Rustem666666/GyverNightLamp/firmware/Schemes/Lamp+TM1637+DFplayer + IR2 + USB  + DS3231 (ESP32).png

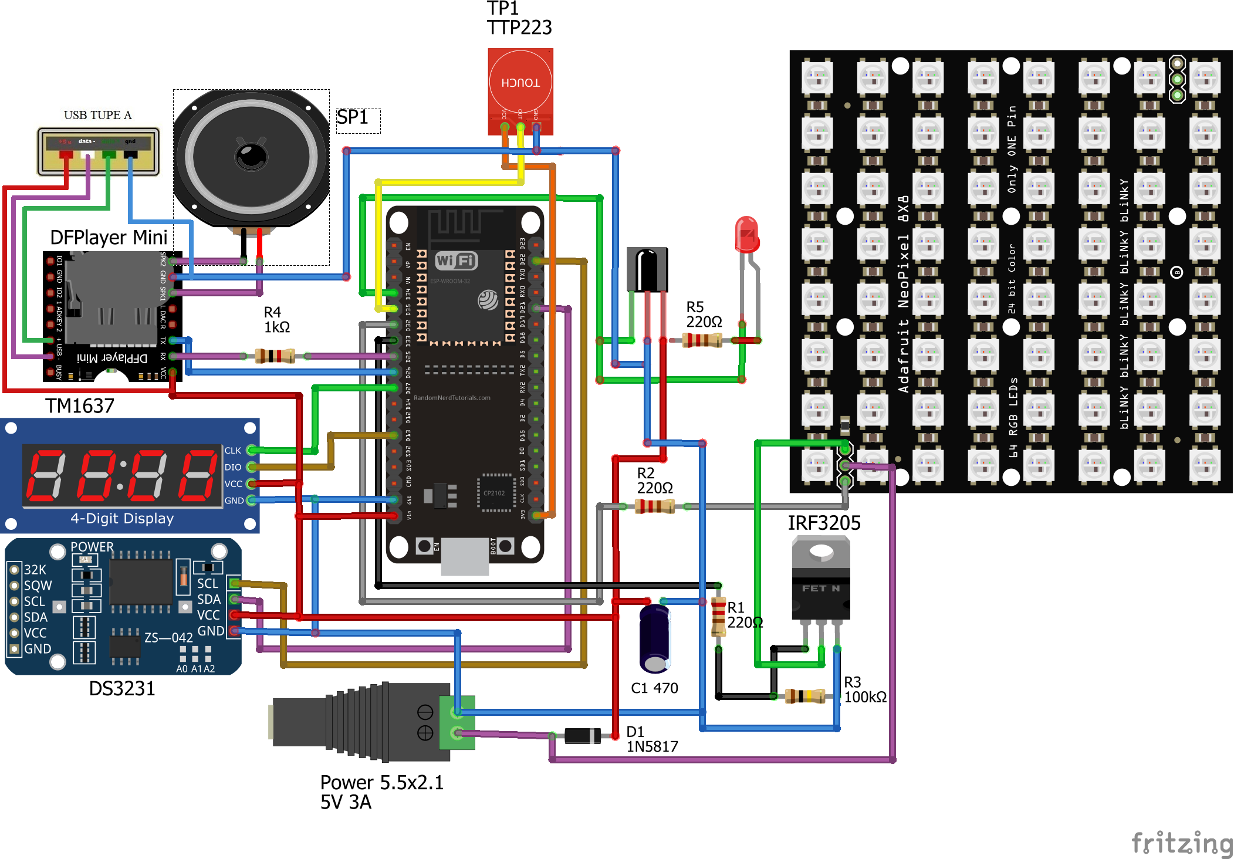
firmware/Schemes/Lamp+TM1637+DFplayer + IR2 + USB + DS3231 (ESP32).png
