Rustem666666/GyverNightLamp/firmware/FieryLedLamp/Constants.h

// Текущая версия : FieryLedLamp v5.4 132 эффекта
// ВНИМАНИЕ!!! Большая часть настроек перенесена в файл data/config и может изменяться в процессе эксплуатации лампы.
// Внимательно читайте файл ПРОЧТИ МЕНЯ!!!.txt и ПРОЧТИ МЕНЯ.doc (тут с картинками)

#pragma once

#define FLL_VERSION           (" Ver.5.4.132")


// ==========  ВНЕШНЕЕ УПРАВЛЕНИЕ  ===============
#define USE_MQTT                    (false)                  // true – используется mqtt клиент, false – нет
#if USE_MQTT
#define MQTT_RECONNECT_TIME   (10U)                         // Время в секундах перед подключением к брокеру MQTT в случае потери подключения
#endif
//#define USE_BLYNK  ("сюда_вставить_токен_из_приложения")  // раскомментируйте эту строку, если вы используете приложение Blynk (для iOS и Android) https://community.alexgyver.ru/threads/nastrojka-programmy-blynk-dlja-fiery-led-lamp.7787/

// =======  МОДУЛИ, ИСПОЛЬЗУЕМЫЕ  ==========
//#define ESP_USE_BUTTON                                      // Закомментировать, если кнопка не используется ((иначе лампа может регистрировать "фантомные" нажатия и некорректно устанавливать яркость)отключается на web странице)
//#define TM1637_USE                                          // Закомментировать, если не используется дисплей TM1637
//#define MP3_PLAYER_USE                                      // Закомментировать, если не используется плеер
//#define IR_RECEIVER_USE                                     // Закомментировать, если не используется ИК ДУ
//#define USE_RTC                                           // Закомментировать, если не используется RTC модуль
#ifdef USE_RTC
#define RTC_3231                                            

#endif
#ifdef TM1637_USE
  #define RTC_ATTACHED_TO_TM                                // для экономии пинов, DS3231 подключается параллельно TM1637
#endif

// =============  НАСТРОЙКА  ====================
#define USE_DEFAULT_SETTINGS_RESET                          // Закомментируйте эту строку, если не требуется, чтобы при загрузке списка эффектов с лампы настройки эффектов смахивали на значение по умолчанию

#define USE_MULTIPLE_LAMPS_CONTROL                          // Добавить код для управления несколькими лампами

//#define MP3_DEBUG                                         // если строка не закомментирована, выводятся отладочные сообщения mp3 player
//#define HEAP_SIZE_PRINT                                   // если строка не закомментирована, будет выводиться размер "купи" (свободного ОЗУ)
//#define GENERAL_DEBUG                                     // если строка не закомментирована, будут выводиться общие отладочные сообщения
#ifdef GENERAL_DEBUG
 //#define MAIN_CYCLES_PER_SECOND                           // Выводит количество главных циклов в секунду. Приблизительно то же, что и FPS. Будет выводиться только вместе с GENERAL_DEBUG
#endif

#define USE_LittleFS                                        // Закомментируйте эту строку, если вместо файловой системы LittlFS хотите использовать файловую систему SPIFFS (устаревшая)

// --- НАСТРОЙКА МР3 ПЛЕЕРА -------------
#ifdef MP3_PLAYER_USE
  //#define CHECK_MP3_CONNECTION                            // Закомментируйте эту строку, если нужно, чтобы лампа не проверяла наличие связи с MP3 плеером.
  //#define DF_PLAYER_IS_ORIGINAL                           // Если используется проигрыватель с чипом, отличным от AS20HGN402, закомментируйте эту строку
  #ifndef  DF_PLAYER_IS_ORIGINAL
    //#define DF_PLAYER_GD3200x                             // Если у вас такой чип в плеере и эта строка не закомментирована, то для озвучивания времени используются разные голоса.
  #endif  //DF_PLAYER_IS_ORIGINAL
#endif  //MP3_PLAYER_USE

// --- НАСТРОЙКА КНОПКИ -----------------
#define BUTTON_CAN_SET_SLEEP_TIMER                          // с этой строчкой, если на лампе набить кнопкой 4х кратно (один раз), лампа мигнёт дважды синим и если она выключена , то включится.
                                                            // Таймер выключения лампы будет установлен на BUTTON_SET_SLEEP_TIMER1 минут. Если на лампе набить кнопкой 3х кратно + удержание 4го нажатия, лампа мигнёт синим трижды и если она выключена , то включится.
                                                            // Таймер выключения лампы будет установлен на BUTTON_SET_SLEEP_TIMER2 минут. Чтобы убрать эту функцию, удалите или закомментируйте эту строчку
#ifdef BUTTON_CAN_SET_SLEEP_TIMER
  #define BUTTON_SET_SLEEP_TIMER1   (5UL)                   
  #define BUTTON_SET_SLEEP_TIMER2   (10UL)
#endif
#define BUTTON_IS_SENSORY     (1)                           // Если у вас не сенсорная, а простая кнопка, поменяйте в этой строке 1 на 0
#define BUTTON_LOCK_ON_START                                // с этой строкой, если в момент включения лампы в розетку успеть нажать кнопку или если вы забудете кнопку подключить, лампа отключит реакцию нажатия кнопки до следующего раза
#ifdef ESP_USE_BUTTON
#define DISPLAY_IP_AT_START                                 // Закомментируйте эту строку, если хотите, чтобы при включении питания и подключении к WiFi лампа один раз выводила свой IP адрес (для ламп с кнопкой)
#else
#define DISPLAY_IP_AT_START                                 // Закомментируйте эту строку, если не хотите, чтобы при включении питания и подключении к WiFi лампа один раз выводила свой IP адрес (для ламп без кнопки)
#endif  //ESP_USE_BUTTON
#if defined (ESP_USE_BUTTON)
#define BUTTON_STEP_TIMEOUT   (100U)                        // каждые BUTTON_STEP_TIMEOUT мс будет генерироваться событие удерживания кнопки (для регулировки яркости)
#define BUTTON_CLICK_TIMEOUT  (500U)                        // максимальное время между нажатиями кнопки в мс, до достижения которого считается серия последовательных нажатий
#if (BUTTON_IS_SENSORY == 1)
  #define BUTTON_SET_DEBOUNCE   (10U)                       // Время антидребезга mS для сенсорной кнопки
#else
  #define BUTTON_SET_DEBOUNCE   (60U)                       // Время антидребезга mS для механической кнопки
#endif
#endif

// --- ВРЕМЯ ---------------------------
#define GET_TIME_FROM_PHONE (5U)                            // с этой строчкой время в лампе само синхронизируется с приложением, когда лампа не имеет или потеряла доступ в интернет на сервер точного времени .
                                                            // для этого нужно использовать приложение FireLamp версии 3.0 или выше, либо другое приложение, которое отправляет время телефона в лампу. 
                                                            // цифра 5U означает, что синхранизация не чаще, чем раз в 5 минут. переход на зимнее время произойдёт только если изменение пришло со смартфона!
#define PHONE_N_MANUAL_TIME_PRIORITY                        // с этой строчкой, если время получено через приложение, то попытки синхронизации с NTP-сервером прекращаются (пригодится тем, у кого возникают проблемы с NTP-сервером)
#define WARNING_IF_NO_TIME      (7U)                        // с этой строчкой лампа будет подмигивать в нижнем ряде светодиодов, когда она не знает, сколько сейчас времени.
                                                            // 7 - это яркость мигающих точек (максимум - 255U), когда лампа выключена
//#define WARNING_IF_NO_TIME_ON_EFFECTS_TOO                 // а если эту строку раскомментировать, то подмигивание будет даже во время работы эффектов. яркость точек будет, как у работающего эффекта
#define USE_NTP                                             // закомментировать или удалить эту строку, если нужно, чтобы лампа не обращалась в интернет на сервер времени (NTP-сервер).
                                                            // Стоит её убрать только в том случае, если в вашей домашней сети нет круглосуточного доступа в интернет.
                                                            // Лампу можно отправить в другой часовой пояс, так как часовой пояс, выставляется на web странице. 
                                                            // Там же чекбоксом выбирается необходимость перехода на летнее время.
#define NTP_INTERVAL          (59 * 60UL * 1000UL)          // интервал синхронизации времени (59 минут)
                                                            // константы DAY_HOURS_BRIGHTNESS и NIGHT_HOURS_BRIGHTNESS используются только, когда матрица выключена, иначе будет использована яркость текущего эффекта
// --- Яркость вспышки ПРЕДУПРЕЖДЕНИЕ showWarning ---
#define WARNING_BRI_DAY    (10U)                            // Яркость вспышки предупреждение днем
#define WARNING_BRI_NIGHT    (5U)                           // Яркость вспышки предупреждения ночью

// --- МАТРИЦА -------------------------
#define CURRENT_LIMIT         (2000U)                       // Лимит потребления матрицы по току в миллиамперах, автоматически управляет яркостью (пожалей свой блок питания!) 0 – выключить лимит

#define WIDTH                 (16)                          // ширина матрицы
#define HEIGHT                (8)                          // высота матрицы

#define COLOR_ORDER           (GRB)                         // порядок цветов на ленте. Если цвет отображается некорректно - меняйте. Начать можно с RGB

// --- РАЗНОЕ -----------------------------
#define ESP_CONF_TIMEOUT        (60U)                       // Время в секундах, которое лампа будет ждать от вас ввода пароля для ОТА обновления (пароль совпадает с паролем точки доступа)
#define INTERNET_CHECK_PERIOD   (60UL)                      // Период повторной проверки наличия интернета в секундах


// ========  РАЗДЕЛЕНИЕ КОНТАКТОВ МОДУЛЯ  ==================================================

// --- ESP_PIN_OUT ESP32 ---  РАЗДЕЛЕНИЕ КОНТАКТОВ МОДУЛЯ ESP32 (ESP8266 смотри ниже) -----
#ifdef ESP32_USED
#define LED_PIN               (32U)                         // Пин ленты
#define BTN_PIN               (35U)                         // Пин кнопки

#define I2C_SDA               (21U)                         // DS3231 SDA pin
#define I2C_SCL               (22U)                         // DS3231 SCL pin

#define MOSFET_PIN            (33U)                         // Пин MOSFET транзистора - может использоваться для управления питанием матрицы/ленты (если раскомментирована строка)
#define MOSFET_LEVEL          (HIGH)                        // логический уровень, в который будет установлен пен MOSFET_PIN, когда матрица включена - HIGH или LOW (если раскомментировать)
//#define ALARM_PIN             (39U)                       // пен состояния будильника – может быть использован для управления любым внешним устройством на время работы будильника (если раскомментировать)
//#define ALARM_LEVEL           (HIGH)                      // логический уровень, в который будет установлен пен ALARM_PIN, когда "рассвет"/будильник включен (если раскомментировать)

#ifdef TM1637_USE
#define DIO                   (13U)                         // TM1637 display DIO pin
#define CLK                   (27U)                         // TM1637 display CLK pin
#endif  //TM1637_USE

#ifdef MP3_PLAYER_USE
 #define MP3_TX_PIN            (25U)                        // Определяет пин TX (RX на плеере) последовательного порта
 #define MP3_RX_PIN            (26U)                        // Определяет пин RX (TX на плеере) последовательного порта
 #endif //MP3_PLAYER_USE
 
#ifdef IR_RECEIVER_USE
  #define IR_RECEIVER_PIN     (34U)                         // Пин ИК сенсора
#endif  //IR_RECEIVER_USE

#else
// --- ESP_PIN_OUT ESP8266 ---  РАЗДЕЛЕНИЕ КОНТАКТОВ МОДУЛЯ ESP8266 (ESP32 смотри выше) ---
#define LED_PIN               (0U)                          // Пин ленты                (D3) 
#define BTN_PIN               (4U)                          // Пин кнопки               (D2)

#define MOSFET_PIN            (16U)                         // Пин MOSFET транзистора (D0) - может использоваться для управления питанием матрицы/ленты (если раскомментирована строка)
#define MOSFET_LEVEL          (HIGH)                        // логический уровень, в который будет установлен пен MOSFET_PIN, когда матрица включена - HIGH или LOW (если раскомментировать)
//#define ALARM_PIN             (15U)                       // Пин состояния будильника – может быть использован для управления любым внешним устройством на время работы будильника (если раскомментировать)
//#define ALARM_LEVEL           (HIGH)                      // логический уровень, в который будет установлен пен ALARM_PIN, когда "рассвет"/будильник включен (если раскомментировать)

#ifdef TM1637_USE
  #define DIO                   (14U)                       // TM1637 DIO на pin (D5)
  #define CLK                   (5U)                        // TM1637 CLK на pin (D1)
#endif  //TM1637_USE

#ifdef RTC_ATTACHED_TO_TM
  #define I2C_SDA               (CLK)
  #define I2C_SCL               (DIO)
#else
  #define I2C_SDA               (5U)                        // DS3231 SDA на GPIO5 (D1)
  #define I2C_SCL               (14U)                       // DS3231 SCL на GPIO14 (D5)
#endif

#ifdef MP3_PLAYER_USE
 #define MP3_TX_PIN            (12U)                        // Определяет пин (D6) TX (RX на плеере) последовательного порта
 #define MP3_RX_PIN            (13U)                        // Определяет пин (D7) RX (TX на плеере) последовательного порта
 #endif //MP3_PLAYER_USE

#ifdef IR_RECEIVER_USE
  #define IR_RECEIVER_PIN     (2U)                          //Пин ИК сенсора D4
#endif  //IR_RECEIVER_USE
#endif

// ==================================================================================================
//#define CONNECTION_ANGLE      (0U)                        // угол подключения: 0 - левый нижний, 1 - левый верхний, 2 - правый верхний, 3 - правый нижний
//#define STRIP_DIRECTION       (0U)                        // направление ленты из угла: 0 - вправо, 1 - вверх, 2 - влево, 3 - вниз
                                                            // при неправильной настройке матрицы вы получите предупреждение "Wrong matrix parameters! Set to default"
// Не используется.                                         // шпаргалка по настройке матрицы здесь: https://alexgyver.ru/wp-content/uploads/2018/11/scheme3.jpg
// Это настраивается в веб-интерфейсе.                      // (но в ней, кажется, перепутаны местами квадратики в 4м столбце, а может, и ещё какие-то)

// =========  ЭФФЕКТЫ  =======================================================================
// == названия и номера эффектов ниже в списке используются на вкладке effectTricker ==
// == если меняете, меняйте и там, и ещё здесь ниже в РЕЕСТРЕ ДОСТУПНЫХ ЭФФЕКТОВ ==

#define EFF_WHITE_COLOR         (  0U)    // Бeлый cвeт
#define EFF_AVRORA              (  1U)    // Аврора
#define EFF_WATERCOLOR          (  2U)    // Акварель
#define EFF_FLOWERRUTA          (  3U)    // Аленький цветочек
#define EFF_BUTTERFLY           (  4U)    // Бабочка
#define EFF_EFF_POOL            (  5U)    // Бассейн
#define EFF_BAMBOO              (  6U)    // Бамбук
#define EFF_MADNESS             (  7U)    // Безумие
#define EFF_BALLROUTINE         (  8U)    // Блуждающий кубик
#define EFF_WATERFALL           (  9U)    // Водопад
#define EFF_WATERFALL_4IN1      ( 10U)    // Водопад 4в1
#define EFF_WAVES               ( 11U)    // Волны
#define EFF_MAGICLANTERN        ( 12U)    // Волшебный Фонарик
#define EFF_WINE                ( 13U)    // Вино
#define EFF_WHIRL               ( 14U)    // Вихри пламени
#define EFF_WHIRL_MULTI         ( 15U)    // Вихри разноцветные
#define EFF_STARFALL            ( 16U)    // Вьюга
#define EFF_STORMY_RAIN         ( 17U)    // Гроза в банке
#define EFF_DNA                 ( 18U)    // ДНК
#define EFF_SMOKE               ( 19U)    // Дым
#define EFF_SMOKE_COLOR         ( 20U)    // Дым разноцветный
#define EFF_SMOKEBALLS          ( 21U)    // Дымовые шашки
#define EFF_LIQUIDLAMP          ( 22U)    // Жидкая лампа
#define EFF_LIQUIDLAMP_AUTO     ( 23U)    // Жидкая лампа авто
#define EFF_SWIRL               ( 24U)    // Завиток
#define EFF_STARS               ( 25U)    // Звезды
#define EFF_NEW_STARS           ( 26U)    // Звезды Новые
#define EFF_ZEBRA               ( 27U)    // Зебра
#define EFF_TIXYLAND            ( 28U)    // Земля Тикси
#define EFF_SNAKES              ( 29U)    // Змейки
#define EFF_FOUNTAIN            ( 30U)    // Источник
#define EFF_DROP_IN_WATER       ( 31U)    // Капли на воде
#define EFF_DROPS               ( 32U)    // Капли на стекле
#define EFF_LLAND               ( 33U)    // Кипение
#define EFF_RINGS               ( 34U)    // Кодовый замок
#define EFF_COMET               ( 35U)    // Комета
#define EFF_COMET_COLOR         ( 36U)    // Комета одноцветная
#define EFF_COMET_TWO           ( 37U)    // Комета двойная
#define EFF_COMET_THREE         ( 38U)    // Комета тройная
#define EFF_CONTACTS            ( 39U)    // Контакты
#define EFF_SPARKLES            ( 40U)    // Конфетти
#define EFF_CUBE2D              ( 41U)    // Кубик Рубика
#define EFF_LAVA                ( 42U)    // Лава
#define EFF_LAVALAMP            ( 43U)    // Лавовая лампа
#define EFF_BUTTERFLYS_LAMP     ( 44U)    // Лампа с мотыльками
#define EFF_FOREST              ( 45U)    // Лес
#define EFF_LUMENJER            ( 46U)    // Люмeньep
#define EFF_MAGMA               ( 47U)    // Магма
#define EFF_PAINTS              ( 48U)    // Масляные краски
#define EFF_MATRIX              ( 49U)    // Матрица
#define EFF_TWINKLES            ( 50U)    // Мерцание
#define EFF_METABALLS           ( 51U)    // Метоболз
#define EFF_WEB_TOOLS           ( 52U)    // Мечта дизайнера
#define EFF_MOSAIC              ( 53U)    // Мозайка
#define EFF_BUTTERFLYS          ( 54U)    // Moтыльки
#define EFF_BBALLS              ( 55U)    // Мячики
#define EFF_BALLS_BOUNCE        ( 56U)    // Мячики без границ
#define EFF_CHRISTMAS_TREE      ( 57U)    // Новогодняя Елка
#define EFF_NIGHTCITY           ( 58U)    // Ночной Город
#define EFF_FIRE                ( 59U)    // Огонь
#define EFF_FIRE_2012           ( 60U)    // Огонь 2012
#define EFF_FIRE_2018           ( 61U)    // Огонь 2018
#define EFF_FIRE_2020           ( 62U)    // Огонь 2020
#define EFF_FIRE_2021           ( 63U)    // Огонь 2021
#define EFF_FIREFLY_TOP         ( 64U)    // Огoнь верховой
#define EFF_FIREFLY             ( 65U)    // Огoнь парящий
#define EFF_FIRESPARKS          ( 66U)    // Огонь с искрами
#define EFF_COLOR_RAIN          ( 67U)    // Осадки
#define EFF_OSCILLATING         ( 68U)    // Осциллятор
#define EFF_CLOUDS              ( 69U)    // Облака
#define EFF_OCEAN               ( 70U)    // Океан
#define EFF_OCTOPUS             ( 71U)    // Осьминог
#define EFF_RAINBOW_STRIPE      ( 72U)    // Павлин
#define EFF_HOURGLASS           ( 73U)    // Песочные часы
#define EFF_PAINTBALL           ( 74U)    // Пейнтбол
#define EFF_PICASSO             ( 75U)    // Пикассо
#define EFF_PLASMA              ( 76U)    // Плазма
#define EFF_SPIDER              ( 77U)    // Плазменная лампа
#define EFF_PLASMA_WAVES        ( 78U)    // Плазменные волны
#define EFF_FLAME               ( 79U)    // Пламя
#define EFF_PLANETEARTH         ( 80U)    // Планета Земля
#define EFF_BY_EFFECT           ( 81U)    // Побочный эффект
#define EFF_POPCORN             ( 82U)    // Попкорн
#define EFF_PRISMATA            ( 83U)    // Призмата
#define EFF_ATTRACT             ( 84U)    // Притяжение
#define EFF_LEAPERS             ( 85U)    // Пpыгyны
#define EFF_PULSE               ( 86U)    // Пульс
#define EFF_PULSE_WHITE         ( 87U)    // Пульс белый
#define EFF_PULSE_RAINBOW       ( 88U)    // Пульс радужный
#define EFF_RADIAL_WAWE         ( 89U)    // Радиальная волна
#define EFF_RAINBOW_VER         ( 90U)    // Радуга
#define EFF_RAINBOW             ( 91U)    // Радуга 3D
#define EFF_RAINBOW_SPOT        ( 92U)    // Радужное Пятно
#define EFF_RAINBOW_RINGS       ( 93U)    // Радужные кольца
#define EFF_SNAKE               ( 94U)    // Радужный змей
#define EFF_RAIN                ( 95U)    // Разноцветный дождь
#define EFF_DANDELIONS          ( 96U)    // Разноцветные одуванчики
#define EFF_RIVERS              ( 97U)    // Реки Ботсваны
#define EFF_LIGHTERS            ( 98U)    // Светлячки
#define EFF_LIGHTER_TRACES      ( 99U)    // Светлячки со шлейфом
#define EFF_FEATHER_CANDLE      (100U)    // Свеча
#define EFF_AURORA              (101U)    // Северное сияние
#define EFF_SERPENTINE          (102U)    // Серпантин
#define EFF_SCANNER             (103U)    // Сканер
#define EFF_SINUSOID3           (104U)    // Синусоид
#define EFF_COLORS              (105U)    // Смена цвета
#define EFF_SNOW                (106U)    // Снегопад
#define EFF_SPECTRUM            (107U)    // Спектрум
#define EFF_SPIRO               (108U)    // Спирали
#define EFF_FLOCK               (109U)    // Стая
#define EFF_FLOCK_N_PR          (110U)    // Стая и хищник
#define EFF_ARROWS              (111U)    // Стрелки
#define EFF_STROBE              (112U)    // Строб.Хаос.Дифузия
#define EFF_SHADOWS             (113U)    // Тени
#define EFF_PACIFIC             (114U)    // Тихий океан
#define EFF_TORNADO             (115U)    // Торнадо
#define EFF_SIMPLE_RAIN         (116U)    // Tyчкa в банке
#define EFF_FIREWORK            (117U)    // Фейерверк
#define EFF_FIREWORK_2          (118U)    // Фейерверк 2
#define EFF_FAIRY               (119U)    // Фея
#define EFF_FONTAN              (120U)    // Фонтан
#define EFF_TRICOLOR            (121U)    // Флаг (Триколор)
#define EFF_COLOR               (122U)    // Цвет
#define EFF_EFF_COLORED_PYTHON  (123U)    // Цветной Питон
#define EFF_EFF_SAND            (124U)    // Цветные драже
#define EFF_COLOR_FRIZZLES      (125U)    // Цветные кудри
#define EFF_EFF_LOTUS           (126U)    // Цветок лотоса
#define EFF_TURBULENCE          (127U)    // Цифровая турбулентность
#define EFF_SPHERES             (128U)    // Шapы
#define EFF_NEXUS               (129U)    // Nexus
#define EFF_EFF_COLOR_FADED     (130U)    // Цвет с затуханием
#define EFF_CLOCK               (131U)    // Часы

#define MODE_AMOUNT         (132U)    // количество режимов

// ============= МАССИВ НАСТРОЕК ЭФФЕКТОВ ПО УМОЛЧАНИЮ ===================
// формат записи:
//{ Яркость, Скорость, Масштаб}

static const uint8_t defaultSettings[][3] PROGMEM = {
  {  10,   1,  50}, // Бeлый cвeт
  {  35,  90,  50}, // Аврора
  {  25, 200,  65}, // Акварель
  {  20, 215,  60}, // Аленький цветочек
  {  20,  11,   3}, // Бабочка
  {  25, 185,  63}, // Бассейн
  {  20, 215,  90}, // Бамбук
  {  35,  20,  60}, // Безумие
  {  20, 150,  50}, // Блуждающий кубик
  {  30, 212,  54}, // Водопад
  {  20, 195,  22}, // Водопад 4в1
  {  40, 233,  80}, // Волны
  {  45, 175,  60}, // Волшебный Фонарик
  {  80, 205,  40}, // Вино
  {  25, 210,   1}, // Вихри пламени
  {  20, 210,  86}, // Вихри разноцветные
  {  55, 191,  54}, // Вьюга
  {  40, 210,   8}, // Гроза в банке
  {  30,  80,  95}, // ДНК
  {  25, 195, 100}, // Дым
  {  25, 190,  30}, // Дым разноцветный
  {  30, 170,  25}, // Дымовые шашки
  {  20, 110,   1}, // Жидкая лампа
  {  20, 124,  39}, // Жидкая лампа авто
  {  30, 195,  70}, // Завиток
  {  25, 215,  99}, // Звезды
  {  25,  18,  26}, // Звезды Новые
  {  15,   8,  21}, // Зебра
  {  20, 212,  76}, // Земля Тикси
  {  20,  40,  15}, // Змейки
  {  25, 233,  30}, // Источник
  {  20, 200,  55}, // Капли на воде
  {  20,  40,  59}, // Капли на стекле
  {  15, 240,  18}, // Кипение
  {  30, 205,  91}, // Кодовый замок
  {  20, 205,  28}, // Комета
  {  20, 212,  69}, // Комета одноцветная
  {  25, 186,  19}, // Комета двойная
  {  25, 186,   9}, // Комета тройная
  {  25, 200,  60}, // Контакты
  {  30, 142,  63}, // Конфетти
  {  45, 222,  92}, // Кубик Рубика
  {  15,   9,  24}, // Лава
  {  15, 240,   1}, // Лавовая лампа
  {  30,  61,  20}, // Лампа с мотыльками
  {  15,  15,  95}, // Лес
  {  20, 200,  40}, // Люмeньep
  {  16, 205,  20}, // Магма
  {  15, 195,  50}, // Масляные краски
  {  25, 186,  23}, // Матрица
  {  25, 235,   4}, // Мерцание
  {  15,  72,   3}, // Метоболз
  {  28,  70,  20}, // Мечта дизайнера
  {  15, 205,  50}, // Мозайка
  {  20,  61,  20}, // Moтыльки
  {  15, 255,  26}, // Мячики
  {  25, 255,  85}, // Мячики без границ
  {  30, 165,  30}, // Новогодняя Елка
  {  35,  50,  25}, // Ночной Город
  {  25, 210,   1}, // Огонь
  {  15, 220,  63}, // Огонь 2012
  {  30, 220,  15}, // Огонь 2018
  {  20, 225,  11}, // Огонь 2020
  {  25, 150,  22}, // Огонь 2021
  {  26, 190,  15}, // Огoнь верховой
  {  30, 200,  15}, // Огoнь парящий
  {  30,  80,  64}, // Огонь с искрами
  {  20, 205, 149}, // Осадки
  {  15, 208, 100}, // Осциллятор
  {  20,  15,  34}, // Облака
  {  20,   8,  12}, // Океан
  {  15, 200,  51}, // Осьминог
  {  20,   5,  12}, // Павлин
  {  20, 150,   1}, // Песочные часы
  {  25, 195,   1}, // Пейнтбол
  {  15, 220,  40}, // Пикассо
  {  10,  20,  35}, // Плазма
  {  10,  30,  82}, // Плазменная лампа
  {  15,  15,  50}, // Плазменные волны
  {  30,  45,   3}, // Пламя
  {  25, 128,  75}, // Планета Земля
  {  40, 165,  30}, // Побочный эффект
  {  10,  70,  16}, // Попкорн
  {  15, 100,  88}, // Призмата
  {  20, 205,  65}, // Притяжение
  {  25, 203,   5}, // Пpыгyны
  {  20, 185,   6}, // Пульс
  {  20, 179,  11}, // Пульс белый
  {  20, 185,  31}, // Пульс радужный
  {  15, 220,  50}, // Радиальная волна
  {  10, 215,  50}, // Радуга
  {  10,  13,  60}, // Радуга 3D
  {  40, 200,  40}, // Радужное Пятно
  {  20, 128,  25}, // Радужные кольца
  {  15, 205, 100}, // Радужный змей
  {  15, 205,   1}, // Разноцветный дождь
  {  20,  50,  90}, // Разноцветные одуванчики
  {  12, 175,  50}, // Реки Ботсваны
  {  15, 180,  23}, // Светлячки
  {  15, 185,  93}, // Светлячки со шлейфом
  {  20, 220,   8}, // Свеча
  {  15, 160,  64}, // Северное сияние
  {  15,  75,  50}, // Серпантин
  {  50, 230,  40}, // Сканер
  {  20, 127,  75}, // Синусоид
  {  25, 240,   1}, // Смена цвета
  {  10, 205,  90}, // Снегопад
  {  25, 175, 100}, // Спектрум
  {  15,  45,   3}, // Спирали
  {  15, 136,   4}, // Стая
  {  15, 128,  80}, // Стая и хищник
  {  80, 165,  40}, // Стрелки
  {  25,   1,  45}, // Строб.Хаос.Дифузия
  {  50, 160,   1}, // Тени
  {  20, 127, 100}, // Тихий океан
  {  15, 127,  50}, // Торнадо
  {  50, 210,   2}, // Tyчкa в банке
  {  25, 180,  70}, // Фейерверк
  {  15, 240,  75}, // Фейерверк 2
  {  20, 212,  85}, // Фея
  {  40, 250,  75}, // Фонтан
  {  20,  55,  13}, // Флаг (Триколор)
  {  20, 240,  65}, // Цвет
  {  20, 127,  92}, // Цветной Питон
  {  15, 195,  80}, // Цветные драже
  {  25, 128,  60}, // Цветные кудри
  {  15, 150,  45}, // Цветок лотоса
  {  15, 215,  35}, // Цифровая турбулентность
  {  20,  50,   5}, // Шapы
  {  25,  85,  20}, // Nexus
  {   2,   1,   3}, // Цвет с затуханием
  {  30, 214,  80}  // Часы
}; // ^-- проверьте, чтобы у предыдущей строки не было запятой после скобки

// ------------ ОШИБАТЬСЯ НЕЛЬЗЯ!!!   ------------------------------------------------

// ============= КОНЕЦ МАССИВА =====

// === ОСТАЛЬНОЕ ДЛЯ РАЗРАБОТЧИКОВ =====

// --- МАТРИЦА -------------------------
// если у вас не обычная матрица, а сборка из ленты или гирлянда, и возникают непонятной природы артефакты в рисунке эффекта, попробуйте менять следующие три строчки
//#define FASTLED_ALLOW_INTERRUPTS      (1)                 // default: 1; // Используйте это, чтобы заставить FastLED разрешить прерывания в безтактовых наборах микросхем (или заставить его запретить), переопределив значение по умолчанию на платформах, которые это поддерживают. Установите значение 1, чтобы разрешить прерывания, или 0, чтобы их запретить.
#define FASTLED_INTERRUPT_RETRY_COUNT   (0)                 // default: 2; // Используйте это, чтобы определить, сколько раз FastLED попытается повторно передать кадр, если он слишком долго прерывается.
#ifdef ESP32_USED
 #define FASTLED_ESP32_RAW_PIN_ORDER
#else
 #define FASTLED_ESP8266_RAW_PIN_ORDER                      // FASTLED_ESP8266_RAW_PIN_ORDER, FASTLED_ESP8266_D1_PIN_ORDER or FASTLED_ESP8266_NODEMCU_PIN_ORDER
#endif

#define NUM_LEDS              (uint16_t)(WIDTH * HEIGHT)
#define SEGMENTS              (1U)                          // диодов в одном "пикселе" (для создания матрицы из кусков ленты). вряд ли эффекты будут корректно работать, если изменить этот параметр

#define DYNAMIC                (0U)   // динамическая задержка для кадров ( будет использоваться бегунок Скорость )
#define SOFT_DELAY             (1U)   // задержка для смены кадров FPSdelay задается програмно прямо в теле эффекта
#define LOW_DELAY             (15U)   // низкая фиксированная задержка для смены кадров
#define HIGH_DELAY            (50U)   // высокая фиксированная задержка для смены кадров
#define DYNAMIC_DELAY_TICK    if (millis() - effTimer >= (256U - modes[currentMode].Speed))
#define HIGH_DELAY_TICK       if (millis() - effTimer >= 50)
#define LOW_DELAY_TICK        if (millis() - effTimer >= 15)
#define MICRO_DELAY_TICK      if (millis() - effTimer >= 2)
#define SOFT_DELAY_TICK       if (millis() - effTimer >= FPSdelay)

#define BRIGHTNESS            (40U)                         // стандартная маскимальная яркость (0-255). используется только в момент включения питания лампы

#define ESP_HTTP_PORT         (80U)                         // номер порта, который будет использоваться во время первой утановки имени WiFi сети (и пароля), к которой потом будет подключаться лампа в режиме WiFi клиента (лучше не менять)
#define ESP_UDP_PORT          (8888U)                       // номер порта, который будет "слушать" UDP сервер во время работы лампы как в режиме WiFi точки доступа, так и в режиме WiFi клиента (лучше не менять)
#define WIFIMAN_DEBUG         (false)                       // вывод отладочных сообщений при подключении к WiFi сети: true - выводятся, false - не выводятся; настройка не зависит от GENERAL_DEBUG
#define OTA                                                 // если строка не закомментирована, модуль будет ждать два последовательных запроса пользователя на прошивку по воздуху (два четрёхкратных нажатия на кнопку)
#ifdef OTA
#define ESP_OTA_PORT          (8266U)                       // номер порта, который будет "прослушиваться" в ожидании команды прошивки по воздуху
#endif

#define RANDOM_SETTINGS_IN_CYCLE_MODE                       // Строка добавлена для совместимости файлов эффектов с версией  86 в 1 (или уже больше) от Сотнег.                                                             
                                                            // этот режим можно включать/выключать на web странице лампы или "секретной" командой. Не удаляйте и не комментируйте эту строку.
#define USE_RANDOM_SETS_IN_APP                              // Строка добавлена для совместимости файлов эффектов с версией  86 в 1 (или уже больше) от Сотнег.                               
                                                            // Этот режим уже поддерживается приложением от Котейка под Андроид. Не удаляйте и не комментируйте эту строку.
#define SUMMER_HOUR           (3U)                          // час (по зимнему времени!), когда заканчивается зимнее время и начинается летнее; [0..23]
#define SUMMER_WEEK_NUM       (week_t::Last)                // номер недели в месяце, когда происходит переход на летнее время (возможные варианты: First - первая, Second - вторая, Third - третья, Fourth - четвёртая, Last - последняя)
#define SUMMER_WEEKDAY        (dow_t::Sun)                  // день недели, когда происходит переход на летнее время (возможные варианты: Mon - пн, Tue - вт, Wed - ср, Thu - чт, Sat - сб, Sun - вс)
#define SUMMER_MONTH          (month_t::Mar)                // месяц, в котором происходит переход на летнее время (возможные варианты: Jan - январь, Feb - февраль, Mar - март, Apr - апрель, May - май, Jun - июнь, Jul - июль, Aug - август, Sep - сентябрь, Oct - октябрь, Nov - ноябрь, Dec - декабрь)
#define SUMMER_TIMEZONE_NAME  ("EEST")                      // обозначение летнего времени; до 5 символов; может быть использовано, если понадобится его вывести после вывода времени; может быть "ЛЕТ"
#define WINTER_HOUR           (4U)                          // час (по летнему времени!), когда заканчивается летнее время и начинается зимнее; [0..23]
#define WINTER_WEEK_NUM       (week_t::Last)                // номер недели в месяце, когда происходит переход на зимнее время (возможные варианты: First - первая, Second - вторая, Third - третья, Fourth - четвёртая, Last - последняя)
#define WINTER_WEEKDAY        (dow_t::Sun)                  // день недели, когда происходит переход на зимнее время (возможные варианты: Mon - пн, Tue - вт, Wed - ср, Thu - чт, Sat - сб, Sun - вс)
#define WINTER_MONTH          (month_t::Oct)                // месяц, в котором происходит переход на зимнее время (возможные варианты: Jan - январь, Feb - февраль, Mar - март, Apr - апрель, May - май, Jun - июнь, Jul - июль, Aug - август, Sep - сентябрь, Oct - октябрь, Nov - ноябрь, Dec - декабрь)
#define WINTER_TIMEZONE_NAME  ("EET")                       // обозначение зимнего времени; до 5 символов; может быть использовано, если понадобится его вывести после вывода времени; может быть "ЗИМ"


// --- РАССВЕТ -------------------------
uint8_t DAWN_BRIGHT ;                                       // максимальная яркость рассвета (0-255)
uint8_t DAWN_TIMEOUT;                                       // сколько рассвет светит после времени будильника, минут. Может быть изменено в установках будильника
// --- ЗАКАТ -------------------------
uint8_t SUNSET_BRIGHT ;                                     // максимальная яркость заката (0-255)


//#define MAX_UDP_BUFFER_SIZE (UDP_TX_PACKET_MAX_SIZE + 1)
// максимальный размер буффера UDP сервера 
// 255 - это максимальное значение, при котором работа с Избранным не будет глючить
// для исходящих сообщений в приложение данное ограничение можно обойти (см. как реализована отправка "LIST"),
// а для входящего списка избранного - хз. пришлось увеличить до максимально возможножного значения. 
// дальше придётся переделывать типы (размеры) переменных в функциях FavoritesManager.h
#define MAX_UDP_BUFFER_SIZE   (MODE_AMOUNT * 2 + 20)        // максимальный размер буффера UDP сервера

#define GENERAL_DEBUG_TELNET  (false)                       // true - отладочные сообщения будут выводиться в telnet вместо Serial порта (для удалённой отладки без подключения usb кабелем)
#define TELNET_PORT           (23U)                         // номер telnet порта

#if defined(GENERAL_DEBUG) && GENERAL_DEBUG_TELNET
WiFiServer telnetServer(TELNET_PORT);                       // telnet сервер
WiFiClient telnet;                                          // обработчик событий telnet клиента
bool telnetGreetingShown = false;                           // признак "показано приветствие в telnet"
#define LOG                   telnet
#else
#define LOG                   Serial
#endif

//================ Дальше только для разработчиков. Не меняйте здесь ничего, если не уверены в результате!!! ===================

//#include <EEPROM.h>
//#include "Types.h"
#define EEPROM_PASSWORD_START_ADDRESS           (0U)            // начальный адрес в EEPROM памяти для записи пароля к роутеру
#define EEPROM_MODES_START_ADDRESS              (0x50U)         // начальный адрес в EEPROM памяти для записи настроек эффектов (яркость, скорость, масштаб)
#define EEPROM_FIRST_RUN_ADDRESS                (0x40U)         // (0x40U) адрес в EEPROM памяти для записи признака первого запуска (определяет необходимость первоначальной записи всех хранимых настроек)
#define EEPROM_MODE_STRUCT_SIZE                 (3U)            // 1 байт - яркость; 1 байт - скорость; 1 байт - масштаб
#define EEPROM_TOTAL_BYTES_USED                 (EEPROM_MODES_START_ADDRESS+MODE_AMOUNT*EEPROM_MODE_STRUCT_SIZE+1)       
#define EEPROM_FIRST_RUN_MARK                   (MODE_AMOUNT-255) // число-метка, если ещё не записно в EEPROM_FIRST_RUN_ADDRESS, значит нужно проинициализировать EEPROM и записать все первоначальные настройки
#define EEPROM_WRITE_DELAY                      (30000UL)       // отсрочка записи в EEPROM после последнего изменения хранимых настроек, позволяет уменьшить количество операций записи в EEPROM
#define SAVE_FILE_DELAY_TIMEOUT                 (15000UL)       // отсрочка записи в файл

//+++++Функции для работы с json файлами+++++++++++++++++++++++++++

#include <ArduinoJson.h>        //Установить из менеджера библиотек версию 5.13.5 !!!. https://arduinojson.org/


#ifdef ESP32_USED
 #ifndef CORE_2_0_X
  #define LittleFS LITTLEFS  // Core 1.0.x
 #endif
#include <FS.h>
#ifdef USE_LittleFS
 #ifdef CORE_2_0_X
  #include <LittleFS.h>     // Core 2.0.x
 #else
  #include <LITTLEFS.h>     // Core 1.0.x
 #endif
#else
  #define LittleFS SPIFFS
  #include <SPIFFS.h>
#endif
#else
 #ifdef USE_LittleFS
  #include <LittleFS.h>
  #define LittleFS LittleFS
 #endif  
#endif

// --- AP (WiFi точка доступа) ---
String AP_NAME ="";                                         // Переменная для имени точки доступа. Задаётся на web странице
String AP_PASS = "";                                        // Переменная для пароля точки доступа. Задаётся на web странице
String LAMP_NAME = "";                                      // Переменная для имени Лампы. Задаётся на web странице
const uint8_t AP_STATIC_IP[] = {192, 168, 4, 1};            // статический IP точки доступа (лучше не менять!)

uint8_t ORIENTATION;                                        // Ориентация матрицы
uint8_t MATRIX_TYPE = 0;                                    // тип матрицы: 0 - зигзаг, 1 - параллельная

uint8_t DONT_TURN_ON_AFTER_SHUTDOWN;                        // Не включать после обесточивания
uint32_t AUTOMATIC_OFF_TIME = (0UL);                        // Автовыключение

char NTP_ADDRESS [32];                                      // Массив для адреси сервера NTP

String configSetup = "{}";                                  // Конфиг лампы

// --- ВЫВОД ВРЕМЕНИ БЕГУЩЕЙ СТРОКОЙ ---
unsigned int NIGHT_HOURS_START;                             // Начало ночного времени
unsigned int NIGHT_HOURS_STOP;                              // Завершение ночного времени
unsigned int DAY_HOURS_BRIGHTNESS;                          // Начало дневного времени
unsigned int NIGHT_HOURS_BRIGHTNESS;                        // Завершение дневного времени

// Функции JSON (ArduinoJSON Version 6.19.4)

// ------------- Чтение значения json String
String jsonRead(String &json, String name) {
  DynamicJsonDocument doc(3072);
  DeserializationError error = deserializeJson(doc, json);
  #ifdef GENERAL_DEBUG
  if (error) {
    LOG.print(F("deserializeJson() failed: "));
    LOG.println(error.f_str());
  }
  #endif
//  deserializeJson(doc, json);
  JsonObject obj = doc.as<JsonObject>();  
  return obj[name].as<String>();
}

// ------------- Чтение значения json int
int jsonReadtoInt(String &json, String name) {
  DynamicJsonDocument doc(3072);
  DeserializationError error = deserializeJson(doc, json);
  #ifdef GENERAL_DEBUG
  if (error) {
    LOG.print(F("deserializeJson() failed: "));
    LOG.println(error.f_str());
  }
  #endif
//  deserializeJson(doc, json);
  return doc[name];
}

// ------------- Запись значения json String
void jsonWrite(String &json, String name, String volume) {
  DynamicJsonDocument doc(3072);
  DeserializationError error = deserializeJson(doc, json);
  #ifdef GENERAL_DEBUG
  if (error) {
    LOG.print(F("deserializeJson() failed: "));
    LOG.println(error.f_str());
  }
  #endif
//  deserializeJson(doc, json);
  doc[name] = volume;
  json = "";
  serializeJson(doc, json);
  //return json;
}

// ------------- Запись значения json int
void jsonWrite(String &json, String name, int volume) {
  DynamicJsonDocument doc(3072);
  DeserializationError error = deserializeJson(doc, json);
  #ifdef GENERAL_DEBUG
  if (error) {
    LOG.print(F("deserializeJson() failed: "));
    LOG.println(error.f_str());
  }
  #endif
//  deserializeJson(doc, json);
  doc[name] = volume;
  json = "";
  serializeJson(doc, json);
  //return json;
}


// ------------- Запись строки в файл
String writeFile(const String& fileName, String& strings ) {
  File configFile = LittleFS.open("/" + fileName, "w");
  if (!configFile) {
    return "Failed to open config file";
  }
  configFile.print(strings);
  //strings.printTo(configFile);
  configFile.close();
  #ifdef GENERAL_DEBUG
  LOG.print (F("\nСохранён файл "));
  LOG.println (fileName);
  #endif  //GENERAL_DEBUG
  return "Write sucsses";
}
void saveConfig (){
  writeFile(F("config.json"), configSetup );
}
// ------------- Чтение файла в строку
String readFile(const String& fileName, size_t len ) {
  File configFile = LittleFS.open("/" + fileName, "r");
  if (!configFile) {
    return "Failed";
  }
  size_t size = configFile.size();
  if (size > len) {
    configFile.close();
    return "Large";
  }
  String temp = configFile.readString();
  configFile.close();
  return temp;
}


#if defined(USE_RANDOM_SETS_IN_APP) || defined(RANDOM_SETTINGS_IN_CYCLE_MODE)
void setModeSettings(uint8_t Scale = 0U, uint8_t Speed = 0U);
#endif //#if defined(USE_RANDOM_SETS_IN_APP) || defined(RANDOM_SETTINGS_IN_CYCLE_MODE)

#ifdef USE_MULTIPLE_LAMPS_CONTROL
void multiple_lamp_control ();
bool repeat_multiple_lamp_control = false;
#endif  //USE_MULTIPLE_LAMPS_CONTROL

uint8_t eff_num_correct [MODE_AMOUNT]; //Корректировка номеров эффектов для разных языков
void Display_Timer (uint8_t argument = 0);
void timeTick();
void Save_File_Changes();
bool FileCopy (const String& SourceFile , const String& TargetFile); // Копирование файлов
void showWarning(CRGB color, uint32_t duration, uint16_t blinkHalfPeriod);

#ifdef ESP32_USED
 uint32_t get_Chip_ID(void){
 uint32_t chipId = 0;
   for(int i=0; i<17; i=i+8) {
     chipId |= ((ESP.getEfuseMac() >> (40 - i)) & 0xff) << i;
   }
   return chipId;
 }
#endif
