Rustem666666/GyverNightLamp/firmware/FieryLedLamp/button.ino

#ifdef ESP_USE_BUTTON

bool brightDirection;
static bool startButtonHolding = false;                     // флаг: кнопка удерживается для изменения яркости/скорости/масштаба лампы кнопкой
static bool Button_Holding = false;


void buttonTick()
{
  if (!buttonEnabled) // события кнопки не обрабатываются, если она заблокирована , но обрабатывается сброс в default
  {
    touch.tick();
    if (touch.isStep() && touch.getHoldClicks() == 14U) {
        LOG.println("\n*** Reset to Default ***");
        showWarning(CRGB::Red, 500, 250U);
        #ifdef ESP32_USED
         esp_task_wdt_reset();
        #else
         ESP.wdtFeed();
        #endif
        setModeSettings();
        updateSets();    
        if(FileCopy (F("/default/config.json"), F("/config.json"))) {
            #ifdef ESP32_USED
             esp_task_wdt_reset();
            #else
             ESP.wdtFeed();
            #endif
            showWarning(CRGB::Green, 500, 250U);
            ESP.restart();
        }
        else {
            #ifdef ESP32_USED
             esp_task_wdt_reset();
            #else
             ESP.wdtFeed();
            #endif
            showWarning(CRGB::Red, 500, 250U);
        }
    }  
    return;
  }

  touch.tick();
  uint8_t clickCount = touch.hasClicks() ? touch.getClicks() : 0U;


  // однократное нажатие
  if (clickCount == 1U)
  {
    if (dawnFlag == 1) {
        #ifdef MP3_PLAYER_USE
        if (alarm_sound_flag) {
           send_command(0x0E,0,0,0); //Пауза
           mp3_stop = true;
           alarm_sound_flag = false;
        }
        else
        #endif  // MP3_PLAYER_USE
        {
            manualOff = true;
            dawnFlag = 2;
            #ifdef TM1637_USE
            clockTicker_blink();
            #endif
            SetBrightness(modes[currentMode].Brightness);
            changePower();
       }
       return;
    }
    else if (sunsetFlag == 1) {
        #ifdef MP3_PLAYER_USE
        if (sunset_sound_flag) {
           send_command(0x0E,0,0,0); //Пауза
           mp3_stop = true;
           sunset_sound_flag = false;
        }
        else
        #endif  // MP3_PLAYER_USE
        {
            manualsOff = true;
            sunsetFlag = 2;
            #ifdef TM1637_USE
            clockTicker_blink();
            #endif
            SetBrightness(modes[currentMode].Brightness);
            changePower();
       }
       return;
    }
    else
    {
      ONflag = !ONflag;
      jsonWrite(configSetup, "Power", ONflag);
      changePower(); // Сначала выключаем матрицу

      if (!ONflag)  {
        timeout_save_file_changes = millis() - SAVE_FILE_DELAY_TIMEOUT;
        if (!FavoritesManager::FavoritesRunning) EepromManager::EepromPut(modes);
        save_file_changes = 7;
        Save_File_Changes();
    }
    else {
        EepromManager::EepromGet(modes);
        timeout_save_file_changes = millis();
        bitSet (save_file_changes, 0);
      }
    }
    loadingFlag = true;

    #if (USE_MQTT)
    if (espMode == 1U)
    {
      MqttManager::needToPublish = true;
    }
    #endif
    #ifdef USE_BLYNK
    updateRemoteBlynkParams();
    #endif
    #ifdef USE_MULTIPLE_LAMPS_CONTROL
    if (ONflag) {
        repeat_multiple_lamp_control = true;
    }
    else {
        multiple_lamp_control ();
    }
    #endif  //USE_MULTIPLE_LAMPS_CONTROL
  }


  // двухкратное нажатие
  if (clickCount == 2U){
     #ifdef MP3_PLAYER_USE
     if (dawnFlag == 1) {            //if (dawnFlag && alarm_sound_flag) {
        //myDFPlayer.pause();
        send_command(0x0E,0,0,0);  //Пауза
        mp3_stop = true;
        alarm_sound_flag = false;
        manualOff = true;
        dawnFlag = 2;
        #ifdef TM1637_USE
        clockTicker_blink();
        #endif
        SetBrightness(modes[currentMode].Brightness);
        changePower();
       }
       else if (sunsetFlag == 1) {
        //myDFPlayer.pause();
        send_command(0x0E,0,0,0);  //Пауза
        mp3_stop = true;
        sunset_sound_flag = false;
        manualsOff = true;
        sunsetFlag = 2;
        #ifdef TM1637_USE
        clockTicker_blink();
        #endif
        SetBrightness(modes[currentMode].Brightness);
        changePower();
       }
       else
       #endif  // MP3_PLAYER_USE
      
  if (ONflag)    
  {
    uint8_t temp = jsonReadtoInt(configSetup, "eff_sel");
    if (Favorit_only)
    {
      uint8_t lastMode = currentMode;
      do 
      {
        if (++temp >= MODE_AMOUNT) temp = 0;
        currentMode = eff_num_correct[temp];
      } while (FavoritesManager::FavoriteModes[currentMode] == 0 && currentMode != lastMode);
      if (currentMode == lastMode) // если ни один режим не добавлен в избранное, всё равно куда-нибудь переключимся
        if (++temp >= MODE_AMOUNT) temp = 0;
        currentMode = eff_num_correct[temp];
    }
    else
      if (++temp >= MODE_AMOUNT) temp = 0;
    currentMode = eff_num_correct[temp];
    jsonWrite(configSetup, "eff_sel", temp);
    jsonWrite(configSetup, "br", modes[currentMode].Brightness);
    jsonWrite(configSetup, "sp", modes[currentMode].Speed);
    jsonWrite(configSetup, "sc", modes[currentMode].Scale);
    SetBrightness(modes[currentMode].Brightness);
    loadingFlag = true;

      if (random_on && FavoritesManager::FavoritesRunning)
        selectedSettings = 1U;

    #if (USE_MQTT)
    if (espMode == 1U)
    {
      MqttManager::needToPublish = true;
    }
    #endif
    #ifdef USE_BLYNK
    updateRemoteBlynkParams();
    #endif
    #ifdef USE_MULTIPLE_LAMPS_CONTROL
    repeat_multiple_lamp_control = true;
    #endif  //USE_MULTIPLE_LAMPS_CONTROL
  }
  }

  // трёхкратное нажатие
  if (ONflag && clickCount == 3U)
  {
    uint8_t temp = jsonReadtoInt(configSetup, "eff_sel");
    if (Favorit_only) 
    {
      uint8_t lastMode = currentMode;
      do
      {
        if (--temp >= MODE_AMOUNT) temp = MODE_AMOUNT - 1;
        currentMode = eff_num_correct[temp];
      } while (FavoritesManager::FavoriteModes[currentMode] == 0 && currentMode != lastMode);
      if (currentMode == lastMode) // если ни один режим не добавлен в избранное, всё равно куда-нибудь переключимся
        if (--temp >= MODE_AMOUNT) temp = MODE_AMOUNT - 1;
        currentMode = eff_num_correct[temp];
    }
    else 
      if (--temp >= MODE_AMOUNT) temp = MODE_AMOUNT - 1;
    currentMode = eff_num_correct[temp];
    jsonWrite(configSetup, "eff_sel", temp);
    jsonWrite(configSetup, "br", modes[currentMode].Brightness);
    jsonWrite(configSetup, "sp", modes[currentMode].Speed);
    jsonWrite(configSetup, "sc", modes[currentMode].Scale);
    SetBrightness(modes[currentMode].Brightness);
    loadingFlag = true;

      if (random_on && FavoritesManager::FavoritesRunning)
        selectedSettings = 1U;

    #if (USE_MQTT)
    if (espMode == 1U)
    {
      MqttManager::needToPublish = true;
    }
    #endif
    #ifdef USE_BLYNK
    updateRemoteBlynkParams();
    #endif
    #ifdef USE_MULTIPLE_LAMPS_CONTROL
    repeat_multiple_lamp_control = true;
    #endif  //USE_MULTIPLE_LAMPS_CONTROL
  }


  // четырёхкратное нажатие
  if (clickCount == 4U)
  {
    #ifdef OTA
    if (otaManager.RequestOtaUpdate())
    {
      ONflag = true;
      jsonWrite(configSetup, "Power", ONflag);
      currentMode = EFF_MATRIX;                             // принудительное включение режима "Матрица" для индикации перехода в режим обновления по воздуху
      jsonWrite(configSetup, "eff_sel", currentMode);
      jsonWrite(configSetup, "br", modes[currentMode].Brightness);
      jsonWrite(configSetup, "sp", modes[currentMode].Speed);
      jsonWrite(configSetup, "sc", modes[currentMode].Scale);
      changePower();
    }
    else
    #endif
    
    #ifdef BUTTON_CAN_SET_SLEEP_TIMER
    //if (!ota)
    {
      if (!dawnFlag) {
        // мигать об успехе операции лучше до вызова changePower(), иначе сперва мелькнут кадры текущего эффекта
        showWarning(CRGB::Blue, 1000, 250U);                    // мигание синим цветом 1 секунду
        if (!ONflag) EepromManager::EepromGet(modes);
        ONflag = true;
        changePower();
        jsonWrite(configSetup, "Power", ONflag);
        jsonWrite(configSetup, "tmr", 1);
        #ifdef USE_BLYNK
        updateRemoteBlynkParams();
        #endif
        TimerManager::TimeToFire = millis() + BUTTON_SET_SLEEP_TIMER1 * 60UL * 1000UL;
        TimerManager::TimerRunning = true;
      }
    }
    #endif //BUTTON_CAN_SET_SLEEP_TIMER 
    ;
  }


  // пятикратное нажатие
  if (clickCount == 5U)                                     // вывод IP на лампу
  {
    if (espMode == 1U)
    {
      loadingFlag = true;
      
      #if defined(MOSFET_PIN) && defined(MOSFET_LEVEL)      // установка сигнала в пин, управляющий MOSFET транзистором, матрица должна быть включена на время вывода текста
      digitalWrite(MOSFET_PIN, MOSFET_LEVEL);
      #endif
      while(!fillString(WiFi.localIP().toString().c_str(), CRGB::White, false)) {
          delay(1);
          #ifdef ESP32_USED
           esp_task_wdt_reset();
          #else
           ESP.wdtFeed();
          #endif
          }
      if (ColorTextFon  & (!ONflag || (currentMode == EFF_COLOR && modes[currentMode].Scale < 3))){
        FastLED.clear();
        delay(1);
        FastLED.show();
      }
      #if defined(MOSFET_PIN) && defined(MOSFET_LEVEL)      // установка сигнала в пин, управляющий MOSFET транзистором, соответственно состоянию вкл/выкл матрицы или будильника
      digitalWrite(MOSFET_PIN, ONflag || (dawnFlag == 1 && !manualOff) ? MOSFET_LEVEL : !MOSFET_LEVEL);
      #endif

      loadingFlag = true;
    }
  else
    {
      loadingFlag = true;
      String str = "Точка доступа 192.168.4.1";
      while(!fillString(str.c_str(), CRGB::White, false)) {
          delay(1);
          #ifdef ESP32_USED
           esp_task_wdt_reset();
          #else
           ESP.wdtFeed();
          #endif
          }
      if (ColorTextFon  & (!ONflag || (currentMode == EFF_COLOR && modes[currentMode].Scale < 3))){
        FastLED.clear();
        delay(1);
        FastLED.show();
      }
      loadingFlag = true;
    }
    #if defined(MOSFET_PIN) && defined(MOSFET_LEVEL)      // установка сигнала в пин, управляющий MOSFET транзистором, соответственно состоянию вкл/выкл матрицы или будильника
      digitalWrite(MOSFET_PIN, ONflag || (dawnFlag == 1 && !manualOff) ? MOSFET_LEVEL : !MOSFET_LEVEL);
    #endif
}


  // шестикратное нажатие
  if (clickCount == 6U)                                     // вывод текущего времени бегущей строкой
  {
    printTime(thisTime, true, ONflag);
  }


  // семикратное нажатие
  if (clickCount == 7U)  // if (ONflag &&                   // смена рабочего режима лампы: с WiFi точки доступа на WiFi клиент или наоборот
  {
    #ifdef RESET_WIFI_ON_ESP_MODE_CHANGE
      if (espMode) wifiManager.resetSettings();                             // сброс сохранённых SSID и пароля (сброс настроек подключения к роутеру)
    #endif
    espMode = (espMode == 0U) ? 1U : 0U;
    jsonWrite(configSetup, "ESP_mode", (int)espMode);
    saveConfig();  

    #ifdef GENERAL_DEBUG
    LOG.print(F("Рабочий режим лампы изменён и сохранён в энергонезависимую память\nНовый рабочий режим: ESP_MODE ="));
    LOG.print(espMode);
    LOG.print(espMode == 0U ? F("WiFi точка доступа") : F("WiFi клиент (подключение к роутеру)"));
    LOG.print("\nРестарт...\n");
    delay(1000);
    #endif

    showWarning(CRGB::Red, 3000U, 500U);                    // мигание красным цветом 3 секунды - смена рабочего режима лампы, перезагрузка
    ESP.restart();
  }

  #ifdef MP3_PLAYER_USE
  
  // Восьмикратное нажатие
  if (clickCount == 8U)  {                                  // Вкл / Откл звука
    if (mp3_player_connect == 4) {
      if (eff_sound_on) {
        eff_sound_on = 0;
        showWarning(CRGB::Yellow, 1000, 250U);                    // мигание желтым цветом 1 секунду
        #ifdef GENERAL_DEBUG
        LOG.println (F("Звук выключен"));
        #endif
      }
      else {
        eff_sound_on = eff_volume;
        showWarning(CRGB::Blue, 1000, 250U);                    // мигание синим цветом 1 секунду
        #ifdef GENERAL_DEBUG
        LOG.println (F("Звук включен"));
        #endif
      }
    }
    else  {
        showWarning(CRGB::Red, 1000, 250U);                    // мигание красным цветом 1 секунду
        #ifdef GENERAL_DEBUG
        LOG.println (F("mp3 player не подключен"));
        #endif
    }
    jsonWrite(configSetup, "on_sound", eff_sound_on > 0 ? 1 : 0);
    #ifdef USE_MULTIPLE_LAMPS_CONTROL
    repeat_multiple_lamp_control = true;
    #endif  //USE_MULTIPLE_LAMPS_CONTROL
  }
  #endif  // MP3_PLAYER_USE

  // кнопка только начала удерживаться
  if (touch.isHolded()) // пускай для выключенной лампы удержание кнопки включает белую лампу
  {
    brightDirection = !brightDirection;
    startButtonHolding = true;
  }


  // кнопка нажата и удерживается
if (touch.isStep()){
  if (ONflag && !Button_Holding)
  {

    int8_t but = touch.getHoldClicks();
        //Serial.println (but);

    switch (but )
    {
      case 0U:                                              // просто удержание (до удержания кнопки кликов не было) - изменение яркости
      {
        uint8_t delta = modes[currentMode].Brightness < 10U // определение шага изменения яркости: при яркости [1..10] шаг = 1, при [11..16] шаг = 3, при [17..255] шаг = 15
          ? 1U
          : 5U;
        modes[currentMode].Brightness =
          constrain(brightDirection
            ? modes[currentMode].Brightness + delta
            : modes[currentMode].Brightness - delta,
          1, 255);
        jsonWrite(configSetup, "br", modes[currentMode].Brightness);
        SetBrightness(modes[currentMode].Brightness);
        #ifdef TM1637_USE
        DisplayFlag = 3;
        Display_Timer(modes[currentMode].Brightness);
        #endif    

        #ifdef GENERAL_DEBUG
        LOG.printf_P(PSTR("Новое значение яркости: %d\n"), modes[currentMode].Brightness);
        #endif
        #ifdef USE_MULTIPLE_LAMPS_CONTROL
        repeat_multiple_lamp_control = true;
        #endif  //USE_MULTIPLE_LAMPS_CONTROL
        break;
      }

      case 1U:                                              // удержание после одного клика - изменение скорости
      {
        modes[currentMode].Speed = constrain(brightDirection ? modes[currentMode].Speed + 1 : modes[currentMode].Speed - 1, 1, 255);
        jsonWrite(configSetup, "sp", modes[currentMode].Speed);
        loadingFlag = true; // без перезапуска эффекта ничего и не увидишь

        #ifdef GENERAL_DEBUG
        LOG.printf_P(PSTR("Новое значение скорости: %d\n"), modes[currentMode].Speed);
        #endif
        #ifdef USE_MULTIPLE_LAMPS_CONTROL
        repeat_multiple_lamp_control = true;
        #endif  //USE_MULTIPLE_LAMPS_CONTROL
        #ifdef TM1637_USE
        DisplayFlag = 3;
        Display_Timer(modes[currentMode].Speed);
        #endif    
        #ifdef USE_MULTIPLE_LAMPS_CONTROL
        repeat_multiple_lamp_control = true;
        #endif  //USE_MULTIPLE_LAMPS_CONTROL
        break;
      }

      case 2U:                                              // удержание после двух кликов - изменение масштаба
      {
        modes[currentMode].Scale = constrain(brightDirection ? modes[currentMode].Scale + 1 : modes[currentMode].Scale - 1, 1, 100);
        jsonWrite(configSetup, "sc", modes[currentMode].Scale);
        loadingFlag = true; // без перезапуска эффекта ничего и не увидишь

        #ifdef GENERAL_DEBUG
        LOG.printf_P(PSTR("Новое значение масштаба: %d\n"), modes[currentMode].Scale);
        #endif
        #ifdef USE_MULTIPLE_LAMPS_CONTROL
        repeat_multiple_lamp_control = true;
        #endif  //USE_MULTIPLE_LAMPS_CONTROL
        #ifdef TM1637_USE
        DisplayFlag = 3;
        Display_Timer(modes[currentMode].Scale);
        #endif
        #ifdef USE_MULTIPLE_LAMPS_CONTROL
        repeat_multiple_lamp_control = true;
        #endif  //USE_MULTIPLE_LAMPS_CONTROL
        break;
      }
      
        #ifdef BUTTON_CAN_SET_SLEEP_TIMER
      case 3U:                                               // Таймер сна 10 мин.
      {
        if(!dawnFlag){
          Button_Holding = true;
          // мигать об успехе операции лучше до вызова changePower(), иначе сперва мелькнут кадры текущего эффекта
          showWarning(CRGB::Blue, 1500U, 250U);                    // мигание синим цветом 1 секунду
          ONflag = true;
          changePower();
          jsonWrite(configSetup, "Power", ONflag);
          jsonWrite(configSetup, "tmr", 1);
          #ifdef USE_BLYNK
          updateRemoteBlynkParams();
          #endif
          TimerManager::TimeToFire = millis() + BUTTON_SET_SLEEP_TIMER2 * 60UL * 1000UL;
          TimerManager::TimerRunning = true;
          break;
        }
        break;
      }
        #endif //BUTTON_CAN_SET_SLEEP_TIMER
        
      case 14U:                                             // Сброс основных настроек, хранящихся в файле config.json
      {
          showWarning(CRGB::Red, 500, 250U);
          #ifdef ESP32_USED
           esp_task_wdt_reset();
          #else
           ESP.wdtFeed();
          #endif
          setModeSettings();
          updateSets();    
          if(FileCopy (F("/default/config.json"), F("/config.json"))){
            #ifdef ESP32_USED
             esp_task_wdt_reset();
            #else
             ESP.wdtFeed();
            #endif
              showWarning(CRGB::Green, 2500, 250U);
              ESP.restart();
          }
          else {
            #ifdef ESP32_USED
             esp_task_wdt_reset();
            #else
             ESP.wdtFeed();
            #endif
              showWarning(CRGB::Red, 2500, 250U);
          }
          break;
      }
      
      case 19U:                                            // Сброс всех настроек в "заводские"
      {
          showWarning(CRGB::Red, 500, 250U);
          #ifdef ESP32_USED
           esp_task_wdt_reset();
          #else
           ESP.wdtFeed();
          #endif
          setModeSettings();
          updateSets();    
          if(FileCopy (F("/default/config.json"), F("/config.json"))) {
            #ifdef ESP32_USED
             esp_task_wdt_reset();
            #else
             ESP.wdtFeed();
            #endif
              showWarning(CRGB::Green, 500, 250U);
          }
          else {
            #ifdef ESP32_USED
             esp_task_wdt_reset();
            #else
             ESP.wdtFeed();
            #endif
              showWarning(CRGB::Red, 500, 250U);
          }
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
          }
          else {
            #ifdef ESP32_USED
             esp_task_wdt_reset();
            #else
             ESP.wdtFeed();
            #endif
             showWarning(CRGB::Red, 500, 250U);
          }
          ESP.restart();
          break;
      }

      default:
        break;
    }       
  }
  else
  {
  if (!Button_Holding ) {
    int8_t but = touch.getHoldClicks();
        //Serial.println (but);

    switch (but )
    {
      case 0U:                                              // просто удержание (до удержания кнопки кликов не было) - белый свет
      {
        Button_Holding = true;
        currentMode = EFF_WHITE_COLOR;
    //String Name = "correct." + jsonRead (configSetup, "lang") + ".json";
    //String Correct = readFile(Name, 2048);
    for ( uint8_t n=0; n< MODE_AMOUNT; n++)
    {
        if (eff_num_correct[n] == currentMode)
        {
            jsonWrite(configSetup, "eff_sel", n);
            break;
        }
    }
        jsonWrite(configSetup, "br", modes[currentMode].Brightness);
        jsonWrite(configSetup, "sp", modes[currentMode].Speed);
        jsonWrite(configSetup, "sc", modes[currentMode].Scale);
        ONflag = true;
        jsonWrite(configSetup, "Power", ONflag);
        changePower();
        #ifdef USE_BLYNK
        updateRemoteBlynkParams();
        #endif
        break;
      }
        #ifdef BUTTON_CAN_SET_SLEEP_TIMER     
      case 3U:
      {
        if(!dawnFlag){
          Button_Holding = true;
          // мигать об успехе операции лучше до вызова changePower(), иначе сперва мелькнут кадры текущего эффекта
          showWarning(CRGB::Blue, 1500U, 250U);                    // мигание синим цветом 1 секунду
          EepromManager::EepromGet(modes);
          ONflag = true;
          changePower();
          jsonWrite(configSetup, "Power", ONflag);
          jsonWrite(configSetup, "tmr", 1);
          #ifdef USE_BLYNK
          updateRemoteBlynkParams();
          #endif
          TimerManager::TimeToFire = millis() + BUTTON_SET_SLEEP_TIMER2 * 60UL * 1000UL;
          TimerManager::TimerRunning = true;
          break;
        }
        break;
      }
        #endif //BUTTON_CAN_SET_SLEEP_TIMER
        
      case 14U:
      {
          showWarning(CRGB::Red, 500, 250U);
          #ifdef ESP32_USED
           esp_task_wdt_reset();
          #else
           ESP.wdtFeed();
          #endif
          if(FileCopy (F("/default/config.json"), F("/config.json"))) {
            #ifdef ESP32_USED
             esp_task_wdt_reset();
            #else
             ESP.wdtFeed();
            #endif
              showWarning(CRGB::Green, 2500, 250U);
              ESP.restart();
          }
          else {
            #ifdef ESP32_USED
             esp_task_wdt_reset();
            #else
             ESP.wdtFeed();
            #endif
              showWarning(CRGB::Red, 2500, 250U);
          }
          break;
      }
      case 19U:
      {
          showWarning(CRGB::Red, 500, 250U);
          #ifdef ESP32_USED
           esp_task_wdt_reset();
          #else
           ESP.wdtFeed();
          #endif
          if(FileCopy (F("/default/config.json"), F("/config.json"))) {
            #ifdef ESP32_USED
             esp_task_wdt_reset();
            #else
             ESP.wdtFeed();
            #endif
              showWarning(CRGB::Green, 500, 250U);
          }
          else {
            #ifdef ESP32_USED
             esp_task_wdt_reset();
            #else
             ESP.wdtFeed();
            #endif
              showWarning(CRGB::Red, 500, 250U);
          }
          if(FileCopy (F("/default/config_cycle.json"), F("/config_cycle.json"))) {
            #ifdef ESP32_USED
             esp_task_wdt_reset();
            #else
             ESP.wdtFeed();
            #endif
              showWarning(CRGB::Green, 500, 250U);
          }
          else {
            #ifdef ESP32_USED
             esp_task_wdt_reset();
            #else
             ESP.wdtFeed();
            #endif
              showWarning(CRGB::Red, 500, 250U);
          }
          if(FileCopy (F("/default/config_sound.json"), F("/config_sound.json"))) {
            #ifdef ESP32_USED
             esp_task_wdt_reset();
            #else
             ESP.wdtFeed();
            #endif
              showWarning(CRGB::Green, 500, 250U);
          }
          else {
            #ifdef ESP32_USED
             esp_task_wdt_reset();
            #else
             ESP.wdtFeed();
            #endif
              showWarning(CRGB::Red, 500, 250U);
          }
          if(FileCopy (F("/default/config_alarm.json"), F("/config_alarm.json"))) {
            #ifdef ESP32_USED
             esp_task_wdt_reset();
            #else
             ESP.wdtFeed();
            #endif
              showWarning(CRGB::Green, 500, 250U);
          }
          else {
            #ifdef ESP32_USED
             esp_task_wdt_reset();
            #else
             ESP.wdtFeed();
            #endif
              showWarning(CRGB::Red, 500, 250U);
          }
          if(FileCopy (F("/default/config_sunset.json"), F("/config_sunset.json"))) {
            #ifdef ESP32_USED
             esp_task_wdt_reset();
            #else
             ESP.wdtFeed();
             #endif
            showWarning(CRGB::Green, 500, 250U);
        }
        else {
            #ifdef ESP32_USED
             esp_task_wdt_reset();
            #else
             ESP.wdtFeed();
            #endif
            showWarning(CRGB::Red, 500, 250U);
        }
          if(FileCopy (F("/default/config_hardware.json"), F("/config_hardware.json"))) {
            #ifdef ESP32_USED
             esp_task_wdt_reset();
            #else
             ESP.wdtFeed();
            #endif
              showWarning(CRGB::Green, 500, 250U);
          }
          else {
            #ifdef ESP32_USED
             esp_task_wdt_reset();
            #else
             ESP.wdtFeed();
            #endif
              showWarning(CRGB::Red, 500, 250U);
          }
          if(FileCopy (F("/default/config_multilamp.json"), F("/config_multilamp.json"))) {
            #ifdef ESP32_USED
             esp_task_wdt_reset();
            #else
             ESP.wdtFeed();
            #endif
              showWarning(CRGB::Green, 500, 250U);
          }
          else {
            #ifdef ESP32_USED
             esp_task_wdt_reset();
            #else
             ESP.wdtFeed();
            #endif
            showWarning(CRGB::Red, 500, 250U);
          }
          if(FileCopy (F("/default/config_ip.json"), F("/config_ip.json"))) {
            #ifdef ESP32_USED
             esp_task_wdt_reset();
            #else
             ESP.wdtFeed();
            #endif
              showWarning(CRGB::Green, 500, 250U);
          }
          else {
            #ifdef ESP32_USED
             esp_task_wdt_reset();
            #else
             ESP.wdtFeed();
            #endif
              showWarning(CRGB::Red, 500, 250U);
          }
          if(FileCopy (F("/default/config_mqtt.json"), F("/config_mqtt.json"))) {
            #ifdef ESP32_USED
             esp_task_wdt_reset();
            #else
             ESP.wdtFeed();
            #endif
              showWarning(CRGB::Green, 500, 250U);
          }
          else {
            #ifdef ESP32_USED
             esp_task_wdt_reset();
            #else
             ESP.wdtFeed();
            #endif
            showWarning(CRGB::Red, 500, 250U);
          }
          ESP.restart();
          break;
      }
      
    }
   }
  }
  }

  // кнопка отпущена после удерживания
  if (ONflag && !touch.isHold() && startButtonHolding)      // кнопка отпущена после удерживания, нужно отправить MQTT сообщение об изменении яркости лампы
  {
    startButtonHolding = false;
    Button_Holding = false;
    loadingFlag = true;

    #if (USE_MQTT)
    if (espMode == 1U)
    {
      MqttManager::needToPublish = true;
    }
    #endif
    
    #ifdef USE_BLYNK
    updateRemoteBlynkParams();
    #endif
    
  }
}
#endif
