Rustem666666/GyverNightLamp/firmware/FieryLedLamp/effectTicker.ino

// Если вы хотите добавить эффекты или сделать им копии для демонстрации на разных настройках, нужно делать это в 5 местах:
// 1. в файле effects.ino - добавляется программный код самого эффекта.
// 2. в файле Constants.h - придумываются названия "EFF_......" и задаются порядковые номера эффектам. В конце указывается общее количество MODE_AMOUNT.
// 3. там же в файле Constants.h ниже - задаётся Реестр эффектов для передачи в приложение. 
//    Он живёт отдельно.  Если у вас приложение не поддерживает запрос списка эффектов у лампы, реестр можно не менять.
// 4. там же в файле Constants.h ещё ниже - задаётся Массив настроек эффектов по умолчанию.
//    Просто добавьте строчку для своего нового эффекта в нужное место. Это тоже не обязательно.
// 5. здесь в файле effectTicker.ino - подключается процедура вызова эффекта на соответствующий ей "EFF_......"
//    Можно подключать один и тот же эффект под разными номерами. Например: EFF_FIRE (24U), EFF_FIRE2 (25U), EFF_FIRE3 (26U). Будет три огня для разных цветов.
// Для удобства изменения всех этих списков и настроек в архиве с прошивкой есть файл "таблица_эффектов.xls". 
// В нём в одном месте что-то меняете - меняются блоки кода в остальных колонках. Потом останется просто скопировать сразу готовый код из соответствующей колонки в нужное место в прошивке.

uint32_t effTimer;

void effectsTick()
{
  if (!dawnFlag)
  if (!sunsetFlag)
  {
    // ------------------------------------- у эффектов до EFF_MATRIX (все перед Матрицей) бегунок Скорость не регулирует задержку между кадрами
    if (ONflag )
    {
      switch (currentMode)
      {

        case EFF_WHITE_COLOR:         HIGH_DELAY_TICK { effTimer = millis(); whiteColorStripeRoutine();    Eff_Tick (); }  break;  // (  0U) Бeлый cвeт
        case EFF_AVRORA:              HIGH_DELAY_TICK { effTimer = millis(); Avrora();                     Eff_Tick (); }  break;  // (  1U) Аврора
        case EFF_WATERCOLOR:          DYNAMIC_DELAY_TICK { effTimer = millis(); Watercolor();                 Eff_Tick (); }  break;  // (  2U) Акварель
        case EFF_FLOWERRUTA:          DYNAMIC_DELAY_TICK { effTimer = millis(); FlowerRuta();                 Eff_Tick (); }  break;  // (  3U) Аленький цветочек
        case EFF_BUTTERFLY:           LOW_DELAY_TICK { effTimer = millis(); butterflyRoutine();           Eff_Tick (); }  break;  // (  4U) Бабочка
        case EFF_EFF_POOL:            DYNAMIC_DELAY_TICK { effTimer = millis(); poolRoutine();                Eff_Tick (); }  break;  // (  5U) Бассейн
        case EFF_BAMBOO :             DYNAMIC_DELAY_TICK { effTimer = millis(); Bamboo();                     Eff_Tick (); }  break;  // (  6U) Бамбук
        case EFF_MADNESS:             HIGH_DELAY_TICK { effTimer = millis(); madnessNoiseRoutine();        Eff_Tick (); }  break;  // (  7U) Безумие
        case EFF_BALLROUTINE:         DYNAMIC_DELAY_TICK { effTimer = millis(); ballRoutine();                Eff_Tick (); }  break;  // (  8U) Блуждающий кубик
        case EFF_WATERFALL:           DYNAMIC_DELAY_TICK { effTimer = millis(); fire2012WithPalette();        Eff_Tick (); }  break;  // (  9U) Водопад
        case EFF_WATERFALL_4IN1:      DYNAMIC_DELAY_TICK { effTimer = millis(); fire2012WithPalette4in1();    Eff_Tick (); }  break;  // ( 10U) Водопад 4в1
        case EFF_WAVES:               DYNAMIC_DELAY_TICK { effTimer = millis(); WaveRoutine();                Eff_Tick (); }  break;  // ( 11U) Волны
        case EFF_MAGICLANTERN:        DYNAMIC_DELAY_TICK { effTimer = millis(); MagicLantern();               Eff_Tick (); }  break;  // ( 12U) Волшебный Фонарик
        case EFF_WINE:                DYNAMIC_DELAY_TICK { effTimer = millis(); colorsWine();                 Eff_Tick (); }  break;  // ( 13U) Вино
        case EFF_WHIRL:               DYNAMIC_DELAY_TICK { effTimer = millis(); whirlRoutine(true);           Eff_Tick (); }  break;  // ( 14U) Вихри пламени
        case EFF_WHIRL_MULTI:         DYNAMIC_DELAY_TICK { effTimer = millis(); whirlRoutine(false);          Eff_Tick (); }  break;  // ( 15U) Вихри разноцветные
        case EFF_STARFALL:            DYNAMIC_DELAY_TICK { effTimer = millis(); stormRoutine2();              Eff_Tick (); }  break;  // ( 16U) Вьюга
        case EFF_STORMY_RAIN:         DYNAMIC_DELAY_TICK { effTimer = millis(); stormyRain();                 Eff_Tick (); }  break;  // ( 17U) Гроза в банке
        case EFF_DNA:                 LOW_DELAY_TICK { effTimer = millis(); DNARoutine();                 Eff_Tick (); }  break;  // ( 18U) ДНК
        case EFF_SMOKE:               DYNAMIC_DELAY_TICK { effTimer = millis(); MultipleStreamSmoke(false);   Eff_Tick (); }  break;  // ( 19U) Дым
        case EFF_SMOKE_COLOR:         DYNAMIC_DELAY_TICK { effTimer = millis(); MultipleStreamSmoke(true);    Eff_Tick (); }  break;  // ( 20U) Дым разноцветный
        case EFF_SMOKEBALLS:          LOW_DELAY_TICK { effTimer = millis(); smokeballsRoutine();          Eff_Tick (); }  break;  // ( 21U) Дымовые шашки
        case EFF_LIQUIDLAMP:          LOW_DELAY_TICK { effTimer = millis(); LiquidLampRoutine(true);      Eff_Tick (); }  break;  // ( 22U) Жидкая лампа
        case EFF_LIQUIDLAMP_AUTO:      LOW_DELAY_TICK { effTimer = millis(); LiquidLampRoutine(false);     Eff_Tick (); }  break;  // ( 23U) Жидкая лампа авто
        case EFF_SWIRL:               DYNAMIC_DELAY_TICK { effTimer = millis(); Swirl();                      Eff_Tick (); }  break;  // ( 24U) Завиток
        case EFF_STARS:               DYNAMIC_DELAY_TICK { effTimer = millis(); EffectStars();                Eff_Tick (); }  break;  // ( 25U) Звезды
        case EFF_NEW_STARS:           LOW_DELAY_TICK { effTimer = millis(); StarsEffect();                Eff_Tick (); }  break;  // ( 26U) Звезды Новые
        case EFF_ZEBRA:               HIGH_DELAY_TICK { effTimer = millis(); zebraNoiseRoutine();          Eff_Tick (); }  break;  // ( 27U) Зебра
        case EFF_TIXYLAND:            DYNAMIC_DELAY_TICK { effTimer = millis(); TixyLand();                   Eff_Tick (); }  break;  // ( 28U) Земля Тикси
        case EFF_SNAKES:              LOW_DELAY_TICK { effTimer = millis(); snakesRoutine();              Eff_Tick (); }  break;  // ( 29U) Змейки
        case EFF_FOUNTAIN:            DYNAMIC_DELAY_TICK { effTimer = millis(); starfield2Routine();          Eff_Tick (); }  break;  // ( 30U) Источник
        case EFF_DROP_IN_WATER:       DYNAMIC_DELAY_TICK { effTimer = millis(); DropInWater();                Eff_Tick (); }  break;  // ( 31U) Капли на воде
        case EFF_DROPS:               LOW_DELAY_TICK { effTimer = millis(); newMatrixRoutine();           Eff_Tick (); }  break;  // ( 32U) Капли на стекле
        case EFF_LLAND:               DYNAMIC_DELAY_TICK { effTimer = millis(); LLandRoutine();               Eff_Tick (); }  break;  // ( 33U) Кипение
        case EFF_RINGS:               DYNAMIC_DELAY_TICK { effTimer = millis(); ringsRoutine();               Eff_Tick (); }  break;  // ( 34U) Кодовый замок
        case EFF_COMET:               DYNAMIC_DELAY_TICK { effTimer = millis(); RainbowCometRoutine();        Eff_Tick (); }  break;  // ( 35U) Комета
        case EFF_COMET_COLOR:         DYNAMIC_DELAY_TICK { effTimer = millis(); ColorCometRoutine();          Eff_Tick (); }  break;  // ( 36U) Комета одноцветная
        case EFF_COMET_TWO:           DYNAMIC_DELAY_TICK { effTimer = millis(); MultipleStream();             Eff_Tick (); }  break;  // ( 37U) Комета двойная
        case EFF_COMET_THREE:         DYNAMIC_DELAY_TICK { effTimer = millis(); MultipleStream2();            Eff_Tick (); }  break;  // ( 38U) Комета тройная
        case EFF_CONTACTS:            DYNAMIC_DELAY_TICK { effTimer = millis(); Contacts();                   Eff_Tick (); }  break;  // ( 39U) Контакты
        case EFF_SPARKLES:            DYNAMIC_DELAY_TICK { effTimer = millis(); sparklesRoutine();            Eff_Tick (); }  break;  // ( 40U) Конфетти
        case EFF_CUBE2D:              DYNAMIC_DELAY_TICK { effTimer = millis(); cube2dRoutine();              Eff_Tick (); }  break;  // ( 41U) Кубик Рубика
        case EFF_LAVA:                HIGH_DELAY_TICK { effTimer = millis(); lavaNoiseRoutine();           Eff_Tick (); }  break;  // ( 42U) Лава
        case EFF_LAVALAMP:            LOW_DELAY_TICK { effTimer = millis(); LavaLampRoutine();            Eff_Tick (); }  break;  // ( 43U) Лавовая лампа
        case EFF_BUTTERFLYS_LAMP:     LOW_DELAY_TICK { effTimer = millis(); butterflysRoutine(false);     Eff_Tick (); }  break;  // ( 44U) Лампа с мотыльками
        case EFF_FOREST:              HIGH_DELAY_TICK { effTimer = millis(); forestNoiseRoutine();         Eff_Tick (); }  break;  // ( 45U) Лес
        case EFF_LUMENJER:            DYNAMIC_DELAY_TICK { effTimer = millis(); lumenjerRoutine();            Eff_Tick (); }  break;  // ( 46U) Люмeньep
        case EFF_MAGMA:               DYNAMIC_DELAY_TICK { effTimer = millis(); magmaRoutine();               Eff_Tick (); }  break;  // ( 47U) Магма
        case EFF_PAINTS:              DYNAMIC_DELAY_TICK { effTimer = millis(); OilPaints();                  Eff_Tick (); }  break;  // ( 48U) Масляные краски
        case EFF_MATRIX:              DYNAMIC_DELAY_TICK { effTimer = millis(); matrixRoutine();              Eff_Tick (); }  break;  // ( 49U) Матрица
        case EFF_TWINKLES:            DYNAMIC_DELAY_TICK { effTimer = millis(); twinklesRoutine();            Eff_Tick (); }  break;  // ( 50U) Мерцание
        case EFF_METABALLS:           LOW_DELAY_TICK { effTimer = millis(); MetaBallsRoutine();           Eff_Tick (); }  break;  // ( 51U) Метоболз
        case EFF_WEB_TOOLS:           SOFT_DELAY_TICK { effTimer = millis(); WebTools();                   Eff_Tick (); }  break;  // ( 52U) Мечта дизайнера
        case EFF_MOSAIC:              DYNAMIC_DELAY_TICK { effTimer = millis(); squaresNdotsRoutine();        Eff_Tick (); }  break;  // ( 53U) Мозайка
        case EFF_BUTTERFLYS:          LOW_DELAY_TICK { effTimer = millis(); butterflysRoutine(true);      Eff_Tick (); }  break;  // ( 54U) Moтыльки
        case EFF_BBALLS:              LOW_DELAY_TICK { effTimer = millis(); BBallsRoutine();              Eff_Tick (); }  break;  // ( 55U) Мячики
        case EFF_BALLS_BOUNCE:        LOW_DELAY_TICK { effTimer = millis(); bounceRoutine();              Eff_Tick (); }  break;  // ( 56U) Мячики без границ
        case EFF_CHRISTMAS_TREE:      DYNAMIC_DELAY_TICK { effTimer = millis(); ChristmasTree();              Eff_Tick (); }  break;  // ( 57U) Новогодняя Елка
        case EFF_NIGHTCITY:           HIGH_DELAY_TICK { effTimer = millis(); NightCity();                  Eff_Tick (); }  break;  // ( 58U) Ночной Город
        case EFF_FIRE:                DYNAMIC_DELAY_TICK { effTimer = millis(); fireRoutine(true);            Eff_Tick (); }  break;  // ( 59U) Огонь
        case EFF_FIRE_2012:           DYNAMIC_DELAY_TICK { effTimer = millis(); fire2012again();              Eff_Tick (); }  break;  // ( 60U) Огонь 2012
        case EFF_FIRE_2018:           DYNAMIC_DELAY_TICK { effTimer = millis(); Fire2018_2();                 Eff_Tick (); }  break;  // ( 61U) Огонь 2018
        case EFF_FIRE_2020:           DYNAMIC_DELAY_TICK { effTimer = millis(); fire2020Routine2();           Eff_Tick (); }  break;  // ( 62U) Огонь 2020
        case EFF_FIRE_2021:           LOW_DELAY_TICK { effTimer = millis(); Fire2021Routine();            Eff_Tick (); }  break;  // ( 63U) Огонь 2021
        case EFF_FIREFLY_TOP:         DYNAMIC_DELAY_TICK { effTimer = millis(); MultipleStream5();            Eff_Tick (); }  break;  // ( 64U) Огoнь верховой
        case EFF_FIREFLY:             DYNAMIC_DELAY_TICK { effTimer = millis(); MultipleStream3();            Eff_Tick (); }  break;  // ( 65U) Огoнь парящий
        case EFF_FIRESPARKS:          HIGH_DELAY_TICK { effTimer = millis(); FireSparks();                 Eff_Tick (); }  break;  // ( 66U) Огонь с искрами
        case EFF_COLOR_RAIN:          DYNAMIC_DELAY_TICK { effTimer = millis(); coloredRain();                Eff_Tick (); }  break;  // ( 67U) Осадки
        case EFF_OSCILLATING:         DYNAMIC_DELAY_TICK { effTimer = millis(); oscillatingRoutine();         Eff_Tick (); }  break;  // ( 68U) Осциллятор
        case EFF_CLOUDS:              HIGH_DELAY_TICK { effTimer = millis(); cloudsNoiseRoutine();         Eff_Tick (); }  break;  // ( 69U) Облака
        case EFF_OCEAN:               HIGH_DELAY_TICK { effTimer = millis(); oceanNoiseRoutine();          Eff_Tick (); }  break;  // ( 70U) Океан
        case EFF_OCTOPUS:             DYNAMIC_DELAY_TICK { effTimer = millis(); Octopus();                    Eff_Tick (); }  break;  // ( 71U) Осьминог
        case EFF_RAINBOW_STRIPE:      HIGH_DELAY_TICK { effTimer = millis(); rainbowStripeNoiseRoutine();  Eff_Tick (); }  break;  // ( 72U) Павлин
        case EFF_HOURGLASS:           DYNAMIC_DELAY_TICK { effTimer = millis(); Hourglass();                  Eff_Tick (); }  break;  // ( 73U) Песочные часы
        case EFF_PAINTBALL:           DYNAMIC_DELAY_TICK { effTimer = millis(); lightBallsRoutine();          Eff_Tick (); }  break;  // ( 74U) Пейнтбол
        case EFF_PICASSO:             DYNAMIC_DELAY_TICK { effTimer = millis(); picassoSelector();            Eff_Tick (); }  break;  // ( 75U) Пикассо
        case EFF_PLASMA:              HIGH_DELAY_TICK { effTimer = millis(); plasmaNoiseRoutine();         Eff_Tick (); }  break;  // ( 76U) Плазма
        case EFF_SPIDER:              LOW_DELAY_TICK { effTimer = millis(); spiderRoutine();              Eff_Tick (); }  break;  // ( 77U) Плазменная лампа
        case EFF_PLASMA_WAVES:        SOFT_DELAY_TICK { effTimer = millis(); Plasma_Waves();               Eff_Tick (); }  break;  // ( 78U) Плазменные волны
        case EFF_FLAME:               LOW_DELAY_TICK { effTimer = millis(); execStringsFlame();           Eff_Tick (); }  break;  // ( 79U) Пламя
        case EFF_PLANETEARTH:         SOFT_DELAY_TICK { effTimer = millis(); PlanetEarth();                Eff_Tick (); }  break;  // ( 80U) Планета Земля
        case EFF_BY_EFFECT:           DYNAMIC_DELAY_TICK { effTimer = millis(); ByEffect();                   Eff_Tick (); }  break;  // ( 81U) Побочный эффект
        case EFF_POPCORN:             LOW_DELAY_TICK { effTimer = millis(); popcornRoutine();             Eff_Tick (); }  break;  // ( 82U) Попкорн
        case EFF_PRISMATA:            LOW_DELAY_TICK { effTimer = millis(); PrismataRoutine();            Eff_Tick (); }  break;  // ( 83U) Призмата
        case EFF_ATTRACT:             DYNAMIC_DELAY_TICK { effTimer = millis(); attractRoutine();             Eff_Tick (); }  break;  // ( 84U) Притяжение
        case EFF_LEAPERS:             DYNAMIC_DELAY_TICK { effTimer = millis(); LeapersRoutine();             Eff_Tick (); }  break;  // ( 85U) Пpыгyны
        case EFF_PULSE:               DYNAMIC_DELAY_TICK { effTimer = millis(); pulseRoutine(2U);             Eff_Tick (); }  break;  // ( 86U) Пульс
        case EFF_PULSE_WHITE:         LOW_DELAY_TICK     { effTimer = millis(); pulseRoutine(8U);             Eff_Tick (); }  break;  // ( 87U) Пульс белый
        case EFF_PULSE_RAINBOW:       DYNAMIC_DELAY_TICK { effTimer = millis(); pulseRoutine(4U);             Eff_Tick (); }  break;  // ( 88U) Пульс радужный
        case EFF_RADIAL_WAWE:         DYNAMIC_DELAY_TICK { effTimer = millis(); RadialWave();                 Eff_Tick (); }  break;  // ( 89U) Радиальная волна
        case EFF_RAINBOW_VER:         DYNAMIC_DELAY_TICK { effTimer = millis(); rainbowRoutine();             Eff_Tick (); }  break;  // ( 90U) Радуга
        case EFF_RAINBOW:             HIGH_DELAY_TICK { effTimer = millis(); rainbowNoiseRoutine();        Eff_Tick (); }  break;  // ( 91U) Радуга 3D
        case EFF_RAINBOW_SPOT:        DYNAMIC_DELAY_TICK { effTimer = millis(); RainbowSpot();                Eff_Tick (); }  break;  // ( 92U) Радужное Пятно
        case EFF_RAINBOW_RINGS:       DYNAMIC_DELAY_TICK { effTimer = millis(); RainbowRings();               Eff_Tick (); }  break;  // ( 93U) Радужные кольца
        case EFF_SNAKE:               DYNAMIC_DELAY_TICK { effTimer = millis(); MultipleStream8();            Eff_Tick (); }  break;  // ( 94U) Радужный змей
        case EFF_RAIN:                DYNAMIC_DELAY_TICK { effTimer = millis(); RainRoutine();                Eff_Tick (); }  break;  // ( 95U) Разноцветный дождь
        case EFF_DANDELIONS:          SOFT_DELAY_TICK  { effTimer = millis(); Dandelions();                 Eff_Tick (); }  break;  // ( 96U) Разноцветные одуванчики
        case EFF_RIVERS:              DYNAMIC_DELAY_TICK { effTimer = millis(); BotswanaRivers();             Eff_Tick (); }  break;  // ( 97U) Реки Ботсваны
        case EFF_LIGHTERS:            DYNAMIC_DELAY_TICK { effTimer = millis(); lightersRoutine();            Eff_Tick (); }  break;  // ( 98U) Светлячки
        case EFF_LIGHTER_TRACES:      DYNAMIC_DELAY_TICK { effTimer = millis(); ballsRoutine();               Eff_Tick (); }  break;  // ( 99U) Светлячки со шлейфом
        case EFF_FEATHER_CANDLE:      DYNAMIC_DELAY_TICK { effTimer = millis(); FeatherCandleRoutine();       Eff_Tick (); }  break;  // (100U) Свеча
        case EFF_AURORA:              HIGH_DELAY_TICK { effTimer = millis(); polarRoutine();               Eff_Tick (); }  break;  // (101U) Северное сияние
        case EFF_SERPENTINE:          HIGH_DELAY_TICK { effTimer = millis(); Serpentine();                 Eff_Tick (); }  break;  // (102U) Серпантин
        case EFF_SCANNER:             DYNAMIC_DELAY_TICK { effTimer = millis(); Scanner();                    Eff_Tick (); }  break;  // (103U) Сканер
        case EFF_SINUSOID3:           HIGH_DELAY_TICK { effTimer = millis(); Sinusoid3Routine();           Eff_Tick (); }  break;  // (104U) Синусоид
        case EFF_COLORS:              HIGH_DELAY_TICK { effTimer = millis(); colorsRoutine2();             Eff_Tick (); }  break;  // (105U) Смена цвета
        case EFF_SNOW:                DYNAMIC_DELAY_TICK { effTimer = millis(); Snowfall();                   Eff_Tick (); }  break;  // (106U) Снегопад
        case EFF_SPECTRUM:            DYNAMIC_DELAY_TICK { effTimer = millis(); Spectrum();                   Eff_Tick (); }  break;  // (107U) Спектрум
        case EFF_SPIRO:               LOW_DELAY_TICK { effTimer = millis(); spiroRoutine();               Eff_Tick (); }  break;  // (108U) Спирали
        case EFF_FLOCK:               LOW_DELAY_TICK { effTimer = millis(); flockRoutine(false);          Eff_Tick (); }  break;  // (109U) Стая
        case EFF_FLOCK_N_PR:          LOW_DELAY_TICK { effTimer = millis(); flockRoutine(true);           Eff_Tick (); }  break;  // (110U) Стая и хищник
        case EFF_ARROWS:              DYNAMIC_DELAY_TICK { effTimer = millis(); arrowsRoutine();              Eff_Tick (); }  break;  // (111U) Стрелки
        case EFF_STROBE:              LOW_DELAY_TICK { effTimer = millis(); StrobeAndDiffusion();         Eff_Tick (); }  break;  // (112U) Строб.Хаос.Дифузия
        case EFF_SHADOWS:             LOW_DELAY_TICK { effTimer = millis(); shadowsRoutine();             Eff_Tick (); }  break;  // (113U) Тени
        case EFF_PACIFIC:             LOW_DELAY_TICK { effTimer = millis(); pacificRoutine();             Eff_Tick (); }  break;  // (114U) Тихий океан
        case EFF_TORNADO:             LOW_DELAY_TICK { effTimer = millis(); Tornado();                    Eff_Tick (); }  break;  // (115U) Торнадо
        case EFF_SIMPLE_RAIN:         DYNAMIC_DELAY_TICK { effTimer = millis(); simpleRain();                 Eff_Tick (); }  break;  // (116U) Tyчкa в банке
        case EFF_FIREWORK:            SOFT_DELAY_TICK { effTimer = millis(); Firework();                   Eff_Tick (); }  break;  // (117U) Фейерверк
        case EFF_FIREWORK_2:          DYNAMIC_DELAY_TICK { effTimer = millis(); fireworksRoutine();           Eff_Tick (); }  break;  // (118U) Фейерверк 2
        case EFF_FAIRY:               DYNAMIC_DELAY_TICK { effTimer = millis(); fairyRoutine();               Eff_Tick (); }  break;  // (119U) Фея
        case EFF_FONTAN:              DYNAMIC_DELAY_TICK { effTimer = millis(); Fountain();                   Eff_Tick (); }  break;  // (120U) Фонтан
        case EFF_TRICOLOR:            LOW_DELAY_TICK { effTimer = millis(); FlagRoutine();                Eff_Tick (); }  break;  // (121U) Флаг (Триколор)
        case EFF_COLOR:               LOW_DELAY_TICK  { effTimer = millis(); colorRoutine();               Eff_Tick (); }  break;  // (122U) Цвет
        case EFF_EFF_COLORED_PYTHON : LOW_DELAY_TICK { effTimer = millis(); Colored_Python();             Eff_Tick (); }  break;  // (123U) Цветной Питон
        case EFF_EFF_SAND:            DYNAMIC_DELAY_TICK { effTimer = millis(); sandRoutine();                Eff_Tick (); }  break;  // (124U) Цветные драже
        case EFF_COLOR_FRIZZLES:      SOFT_DELAY_TICK { effTimer = millis(); ColorFrizzles();              Eff_Tick (); }  break;  // (125U) Цветные кудри
        case EFF_EFF_LOTUS:           DYNAMIC_DELAY_TICK { effTimer = millis(); LotusFlower();                Eff_Tick (); }  break;  // (126U) Цветок лотоса
        case EFF_TURBULENCE:          DYNAMIC_DELAY_TICK { effTimer = millis(); Turbulence();                 Eff_Tick (); }  break;  // (127U) Цифровая турбулентность
        case EFF_SPHERES:             LOW_DELAY_TICK { effTimer = millis(); spheresRoutine();             Eff_Tick (); }  break;  // (128U) Шapы
        case EFF_NEXUS:               LOW_DELAY_TICK { effTimer = millis(); nexusRoutine();               Eff_Tick (); }  break;  // (129U) Nexus
        case EFF_EFF_COLOR_FADED:     LOW_DELAY_TICK { effTimer = millis(); colorFaded();                 Eff_Tick (); }  break;  // (130U) Цвет с затуханием
        case EFF_CLOCK:               DYNAMIC_DELAY_TICK { effTimer = millis(); clockRoutine();               Eff_Tick (); }  break;  // (131U) Часы

      }
      #ifdef WARNING_IF_NO_TIME_ON_EFFECTS_TOO
        if (!timeSynched)
          noTimeWarning();
      #endif
    }
    #ifdef WARNING_IF_NO_TIME
    else if (!timeSynched && !ONflag && !((uint8_t)millis())){
      noTimeWarningShow();
    }
    #endif
  }
}

void changePower()
{
  uint8_t k;
  if (dawnFlag == 2) {
      k = DAWN_BRIGHT;
      //Serial.print("dawnFlag = ");
      //Serial.println(dawnFlag);
      //dawnFlag = 0;
  }
  else if (sunsetFlag == 2) {
      k = SUNSET_BRIGHT;
  }
  else  if (AutoBrightness && !day_night)      
          k = constrain(modes[currentMode].Brightness >> AutoBrightness, 1, 100); // Автоматическая яркость
       else
         k = modes[currentMode].Brightness;

  if (ONflag && !dawnFlag && !sunsetFlag)
  {
    effectsTick();
    #if defined(MOSFET_PIN) && defined(MOSFET_LEVEL)      // установка сигнала в пин, управляющий MOSFET транзистором
    digitalWrite(MOSFET_PIN, MOSFET_LEVEL);
    #endif 
    for (uint8_t i = 0U; i < k; i = constrain(i + (k < 60 ? 1 : 4), 0, k))
    {
      FastLED.setBrightness(i);
      FastLED.show();
      delay(1);
    }
    SetBrightness(modes[currentMode].Brightness);
    delay(2);
    FastLED.show();
  }
  else
  {
    if(dawnFlag != 2) effectsTick();
    else dawnFlag = 0;
    for (uint8_t i = k; i > 0; i = constrain(i - (k < 60 ? 1 : 4), 0, k))
    {
      FastLED.setBrightness(i);
      delay(1);
      FastLED.show();
    }
    FastLED.clear();
    delay(2);
    FastLED.show();
    #if defined(MOSFET_PIN) && defined(MOSFET_LEVEL)      // установка сигнала в пин, управляющий MOSFET транзистором
    digitalWrite(MOSFET_PIN, !MOSFET_LEVEL);
    #endif
    if (ONflag) 
    {
        changePower();
        return;
    }
  }
// Сброс таймера автоотключения
  TimerManager::TimerRunning = false;
  TimerManager::TimerHasFired = false;
  TimerManager::TimeToFire = 0ULL;
  jsonWrite(configSetup, "tmr", 0);
    if (ONflag && AUTOMATIC_OFF_TIME) {
      TimerManager::TimerRunning = true;
      TimerManager::TimeToFire = millis() + AUTOMATIC_OFF_TIME;
    }  
  if (!ONflag && FavoritesManager::UseSavedFavoritesRunning == 0U) // если выбрана опция Сохранять состояние (вкл/выкл) "избранного",
  {                                                                // то ни выключение модуля, ни выключение матрицы не сбрасывают текущее состояние (вкл/выкл) "избранного"
      FavoritesManager::TurnFavoritesOff();
      jsonWrite(configSetup, "cycle_on", 0);
  }

  #if (USE_MQTT)
  if (espMode == 1U)
  {
    MqttManager::needToPublish = true;
  }
  #endif
else
  uint8_t k;
  if (sunsetFlag == 2) {
      k = SUNSET_BRIGHT;
  }
  else  if (AutoBrightness && !day_night)      
          k = constrain(modes[currentMode].Brightness >> AutoBrightness, 1, 100); // Автоматическая яркость
       else
         k = modes[currentMode].Brightness;

  if (ONflag && !sunsetFlag)
  {
    effectsTick();
    for (uint8_t i = 0U; i < k; i = constrain(i + (k < 60 ? 1 : 4), 0, k))
    {
      FastLED.setBrightness(i);
      FastLED.show();
      delay(1);
    }
    SetBrightness(modes[currentMode].Brightness);
    delay(2);
    FastLED.show();
  }
  else
  {
    if(sunsetFlag != 2) effectsTick();
    else sunsetFlag = 0;
    for (uint8_t i = k; i > 0; i = constrain(i - (k < 60 ? 1 : 4), 0, k))
    {
      FastLED.setBrightness(i);
      delay(1);
      FastLED.show();
    }
    FastLED.clear();
    delay(2);
    FastLED.show();
    if (ONflag) 
    {
        changePower();
        return;
    }
  }
  // Сброс таймера автоотключения
  TimerManager::TimerRunning = false;
  TimerManager::TimerHasFired = false;
  TimerManager::TimeToFire = 0ULL;
  jsonWrite(configSetup, "tmr", 0);
    if (ONflag && AUTOMATIC_OFF_TIME) {
      TimerManager::TimerRunning = true;
      TimerManager::TimeToFire = millis() + AUTOMATIC_OFF_TIME;
    }  
  if (!ONflag && FavoritesManager::UseSavedFavoritesRunning == 0U) // если выбрана опция Сохранять состояние (вкл/выкл) "избранного",
  {                                                                // то ни выключение модуля, ни выключение матрицы не сбрасывают текущее состояние (вкл/выкл) "избранного"
      FavoritesManager::TurnFavoritesOff();
      jsonWrite(configSetup, "cycle_on", 0);
  }

  #if (USE_MQTT)
  if (espMode == 1U)
  {
    MqttManager::needToPublish = true;
  }
  #endif
}

#ifdef WARNING_IF_NO_TIME
void noTimeWarning() {
  for (uint8_t i = 0; i < WIDTH; i++) leds[XY(i, 0U)] = CRGB::Black;
  uint8_t z = millis() / 1000U;
  #ifdef USE_NTP
    leds[XY(z % WIDTH , 0U)] = espMode ? CRGB::Red : CRGB::Blue; // если при включенном NTP время не получено, будем красным цветом мигать
    leds[XY((z + WIDTH / 2U) % WIDTH , 0U)] = espMode ? CRGB::Red : CRGB::Blue;
  #else  
    leds[XY(z % WIDTH , 0U)] = espMode ? CRGB::Yellow : CRGB::Blue; // иначе скромно жёлтым - нормальная ситуация при отсутствии NTP
    leds[XY((z + WIDTH / 2U) % WIDTH , 0U)] = espMode ? CRGB::Yellow : CRGB::Blue;
  #endif //USE_NTP
}
void noTimeWarningShow() {
  noTimeWarning();
  FastLED.setBrightness(WARNING_IF_NO_TIME);
  FastLED.show();
}
void noTimeClear() {
  if (!timeSynched) {
    for (uint8_t i = 0; i < WIDTH; i++) 
       leds[XY(i, 0U)] = CRGB::Black; 
    FastLED.show();
  }
}
#endif //WARNING_IF_NO_TIME

void Eff_Tick () {
  #ifdef MP3_PLAYER_USE
    mp3_folder=effects_folders[currentMode];
  #endif  // MP3_PLAYER_USE
  #ifdef USE_MULTIPLE_LAMPS_CONTROL
    if (repeat_multiple_lamp_control)  {
        for ( uint8_t n = 0; n < MODE_AMOUNT; n++)
        {
            if (eff_num_correct[n] == currentMode) {
                jsonWrite(configSetup, "eff_sel", n);
                break;
            }
        }
        #ifdef MP3_PLAYER_USE
        if (mp3_player_connect == 4) {
          mp3_loop();
          jsonWrite(configSetup, "fold_sel", CurrentFolder);
        }
        #endif  // MP3_PLAYER_USE
        jsonWrite(configSetup, "br", modes[currentMode].Brightness);
        jsonWrite(configSetup, "sp", modes[currentMode].Speed);
        jsonWrite(configSetup, "sc", modes[currentMode].Scale);          
        multiple_lamp_control ();
        repeat_multiple_lamp_control = false;
    }
    #endif  //USE_MULTIPLE_LAMPS_CONTROL

  if (RuninTextOverEffects)
  {
    if (RuninTextOverEffects > 60 || ((thisTime % RuninTextOverEffects == 0U) && Last_Time_RuninText != thisTime) || !Fill_String)
      {
        Last_Time_RuninText = thisTime;
        Fill_String = fillString(TextTicker, CHSV(ColorRunningText, 255U, 255U), true);
      }
  }
  
  FastLED.show();
}
