Rustem666666/GyverNightLamp/firmware/FieryLedLamp/utility.ino

// служебные функции

// залить все
void fillAll(CRGB color)
{
  for (int16_t i = 0; i < NUM_LEDS; i++)
    leds[i] = color;
}

// функция отрисовки точки по координатам X Y
void drawPixelXY(int8_t x, int8_t y, CRGB color)
{
  if (x < 0 || x > (WIDTH - 1) || y < 0 || y > (HEIGHT - 1)) return;
  uint32_t thisPixel = XY((uint8_t)x, (uint8_t)y) * SEGMENTS;
  for (uint8_t i = 0; i < SEGMENTS; i++)
  {
    leds[thisPixel + i] = color;
  }
}

// функция получения цвета пикселя по его номеру
uint32_t getPixColor(uint32_t thisSegm)
{
  uint32_t thisPixel = thisSegm * SEGMENTS;
  if (thisPixel > NUM_LEDS - 1) return 0;
  return (((uint32_t)leds[thisPixel].r << 16) | ((uint32_t)leds[thisPixel].g << 8 ) | (uint32_t)leds[thisPixel].b); // а почему не просто return (leds[thisPixel])?
}

// функция получения цвета пикселя в матрице по его координатам
uint32_t getPixColorXY(uint8_t x, uint8_t y)
{
  return getPixColor(XY(x, y));
}

// ************* НАСТРОЙКА МАТРИЦЫ *****
/*
#if (CONNECTION_ANGLE == 0 && STRIP_DIRECTION == 0)
#define _WIDTH WIDTH
#define THIS_X x
#define THIS_Y y

#elif (CONNECTION_ANGLE == 0 && STRIP_DIRECTION == 1)
#define _WIDTH HEIGHT
#define THIS_X y
#define THIS_Y x

#elif (CONNECTION_ANGLE == 1 && STRIP_DIRECTION == 0)
#define _WIDTH WIDTH
#define THIS_X x
#define THIS_Y (HEIGHT - y - 1)

#elif (CONNECTION_ANGLE == 1 && STRIP_DIRECTION == 3)
#define _WIDTH HEIGHT
#define THIS_X (HEIGHT - y - 1)
#define THIS_Y x

#elif (CONNECTION_ANGLE == 2 && STRIP_DIRECTION == 2)
#define _WIDTH WIDTH
#define THIS_X (WIDTH - x - 1)
#define THIS_Y (HEIGHT - y - 1)

#elif (CONNECTION_ANGLE == 2 && STRIP_DIRECTION == 3)
#define _WIDTH HEIGHT
#define THIS_X (HEIGHT - y - 1)
#define THIS_Y (WIDTH - x - 1)

#elif (CONNECTION_ANGLE == 3 && STRIP_DIRECTION == 2)
#define _WIDTH WIDTH
#define THIS_X (WIDTH - x - 1)
#define THIS_Y y

#elif (CONNECTION_ANGLE == 3 && STRIP_DIRECTION == 1)
#define _WIDTH HEIGHT
#define THIS_X y
#define THIS_Y (WIDTH - x - 1)

#else
!!!!!!!!!!!!!!!!!!!!!!!!!!!   смотрите инструкцию: https://alexgyver.ru/wp-content/uploads/2018/11/scheme3.jpg
!!!!!!!!!!!!!!!!!!!!!!!!!!!   такого сочетания CONNECTION_ANGLE и STRIP_DIRECTION не бывает
#define _WIDTH WIDTH
#define THIS_X x
#define THIS_Y y
#pragma message "Wrong matrix parameters! Set to default"

#endif
*/
// получить номер пикселя в ленте по координатам
// библиотека FastLED тоже использует эту функцию
uint16_t XY(uint8_t x, uint8_t y)
{
 uint8_t THIS_X;
 uint8_t THIS_Y;
 uint8_t _WIDTH = WIDTH;
 
 switch (ORIENTATION)
 {
  case 0: THIS_X = x;                   //CONNECTION_ANGLE == 0 && STRIP_DIRECTION == 0
          THIS_Y =y;
          break;
  case 1: _WIDTH = HEIGHT;              //CONNECTION_ANGLE == 0 && STRIP_DIRECTION == 1
          THIS_X = y;
          THIS_Y = x;
          break;
  case 2: THIS_X = x;                   //CONNECTION_ANGLE == 1 && STRIP_DIRECTION == 0
          THIS_Y = (HEIGHT - y - 1);
          break;
  case 3: _WIDTH = HEIGHT;              //CONNECTION_ANGLE == 1 && STRIP_DIRECTION == 3
          THIS_X = (HEIGHT - y - 1);
          THIS_Y = x;
          break;
  case 4: THIS_X = (WIDTH - x - 1);     //CONNECTION_ANGLE == 2 && STRIP_DIRECTION == 2
          THIS_Y = (HEIGHT - y - 1);
          break;
  case 5: _WIDTH = HEIGHT;              //CONNECTION_ANGLE == 2 && STRIP_DIRECTION == 3
          THIS_X = (HEIGHT - y - 1);
          THIS_Y = (WIDTH - x - 1);
          break;
  case 6: THIS_X = (WIDTH - x - 1);     //CONNECTION_ANGLE == 3 && STRIP_DIRECTION == 2
          THIS_Y =y;
          break;
  case 7: _WIDTH = HEIGHT;              //CONNECTION_ANGLE == 3 && STRIP_DIRECTION == 1
          THIS_X = y;
          THIS_Y = (WIDTH - x - 1);
          break;
  default : THIS_X = x;                 // !! смотрите инструкцию: https://alexgyver.ru/wp-content/uploads/2018/11/scheme3.jpg
            THIS_Y =y;                  // !! такого сочетания CONNECTION_ANGLE и STRIP_DIRECTION не бывает
            break;
 }
 
  if (!(THIS_Y & 0x01) || MATRIX_TYPE)               // Even rows run forwards
    return (THIS_Y * _WIDTH + THIS_X);
  else                                                  
    return (THIS_Y * _WIDTH + _WIDTH - THIS_X - 1);  // Odd rows run backwards
}

// если у вас матрица необычной формы с зазорами/вырезами, либо просто маленькая, тогда вам придётся переписать функцию XY() под себя
// массив для переадресации можно сформировать на этом онлайн-сервисе: https://macetech.github.io/FastLED-XY-Map-Generator/
// или ту по-русски: https://firelamp.pp.ua/matrix_generator/
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
